sicoco/Minicranebot/stl/wheel base.stl

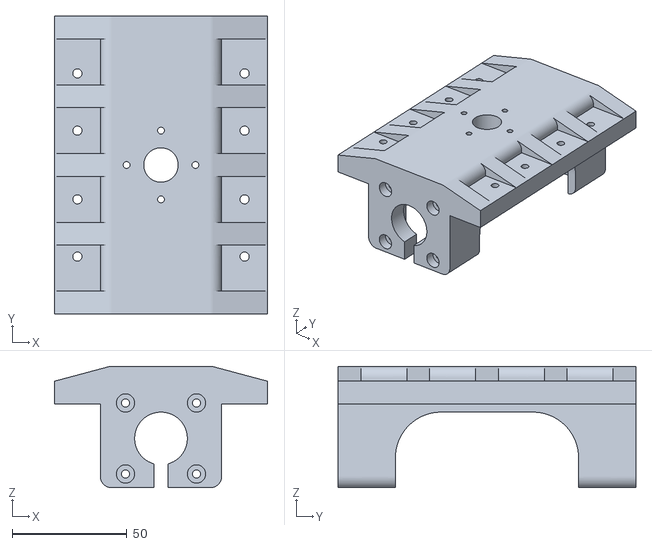
[picture p17: CAD file, 2018-08-06]
stl/wheel base.stl
93.0 x 130.0 x 53.0
