sicoco/Minicranebot/stl/wedge.stl

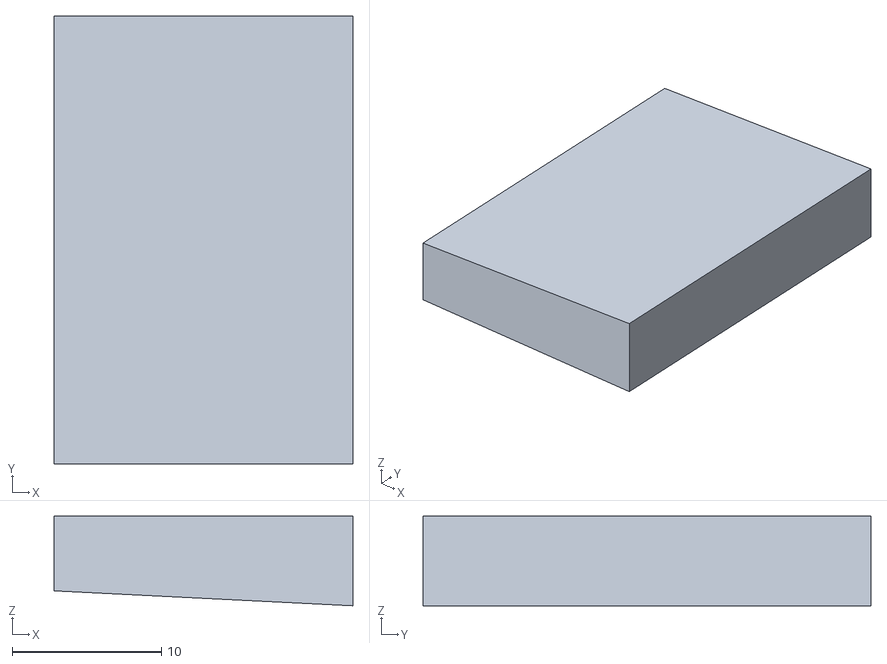
[picture p18: CAD file, 2018-07-30]
stl/wedge.stl
20.0 x 30.0 x 6.00
