sicoco/Minicranebot/stl/wedge v2.stl

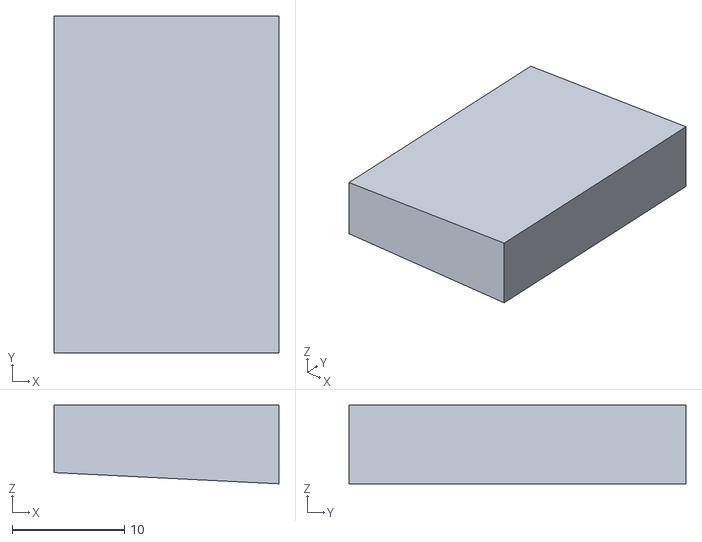
[picture p19: CAD file, 2018-07-30]
stl/wedge v2.stl
20.0 x 30.0 x 7.00
