sicoco/Minicranebot/stl/flex gripper mirror.stl

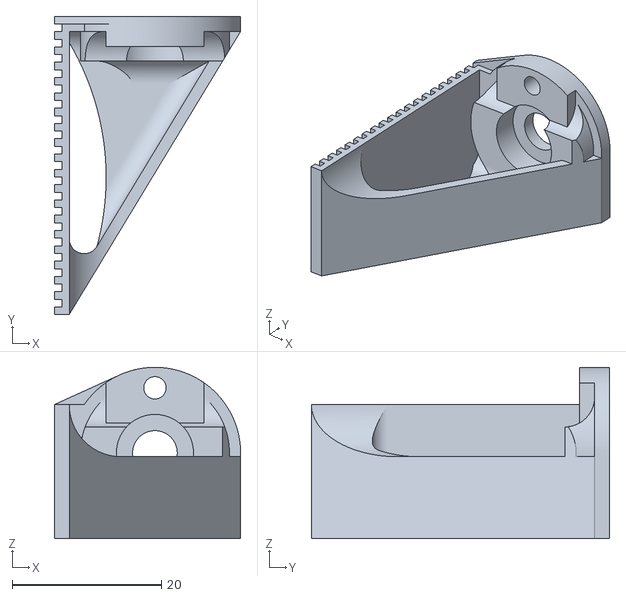
[picture p20: CAD file, 2018-07-27]
stl/flex gripper mirror.stl
25.0 x 40.0 x 23.0
