sicoco/Minicranebot/stl/hook.stl

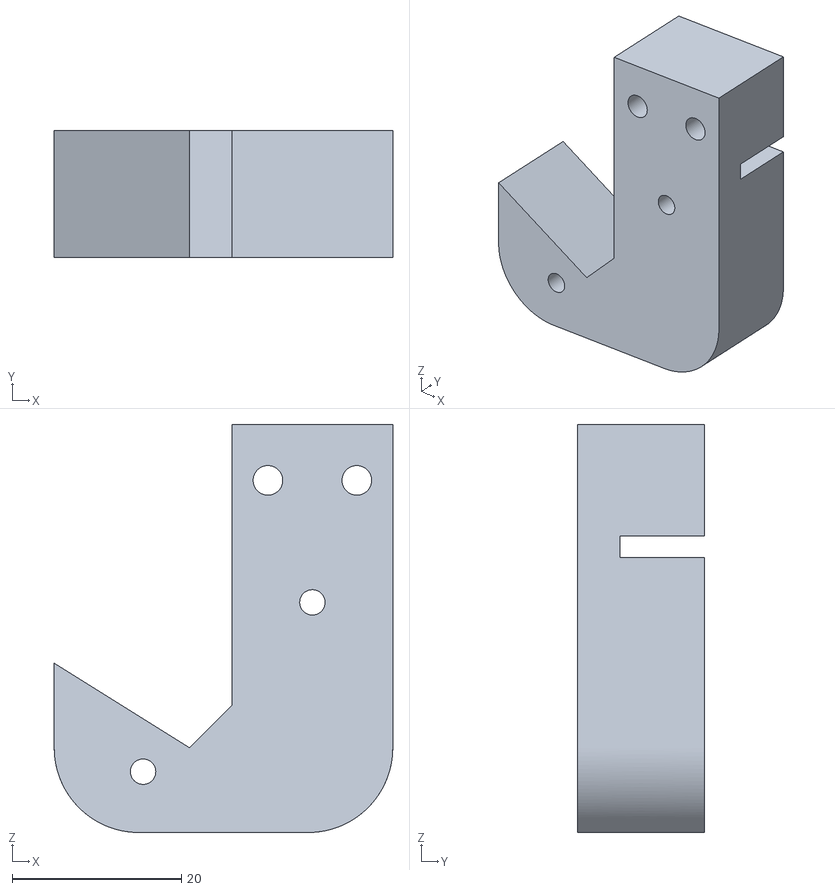
[picture p21: CAD file, 2018-07-27]
stl/hook.stl
40.0 x 15.0 x 48.2
