sicoco/Minicranebot/stl/aligner arm2.stl

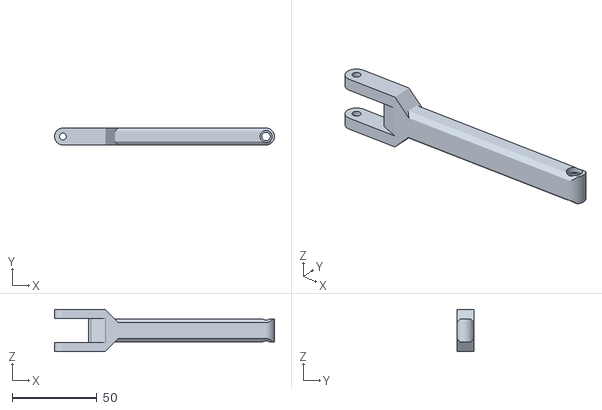
[picture p22: CAD file, 2018-07-27]
stl/aligner arm2.stl
130.0 x 10.0 x 25.0
