sicoco/Minicranebot/stl/waist encoder fixture.stl

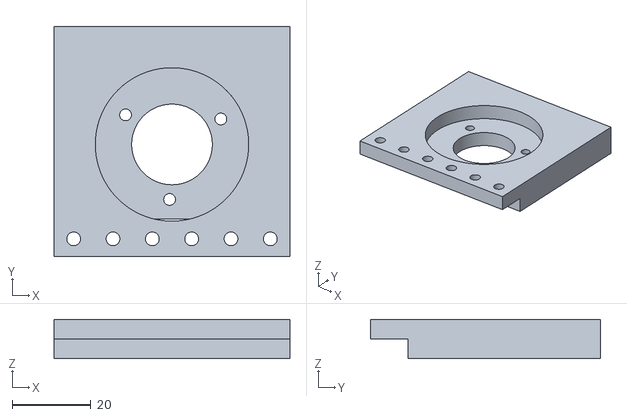
[picture p23: CAD file, 2018-07-27]
stl/waist encoder fixture.stl
60.0 x 58.5 x 10.00
