sicoco/Minicranebot/stl/tentacle block v2.stl

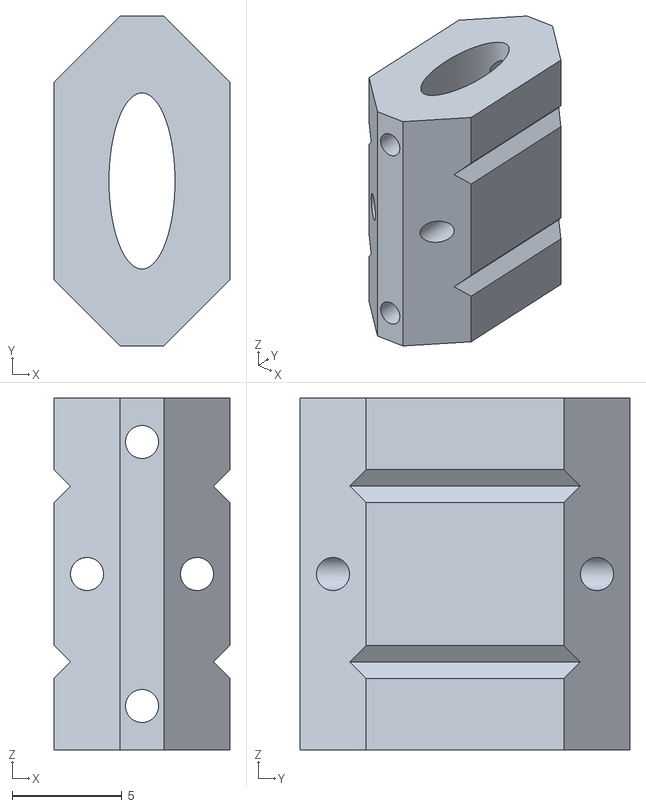
[picture p24: CAD file, 2018-07-27]
stl/tentacle block v2.stl
8.00 x 15.0 x 16.0
