sicoco/Minicranebot/stl/long potentiometer shaft coupler v1.stl

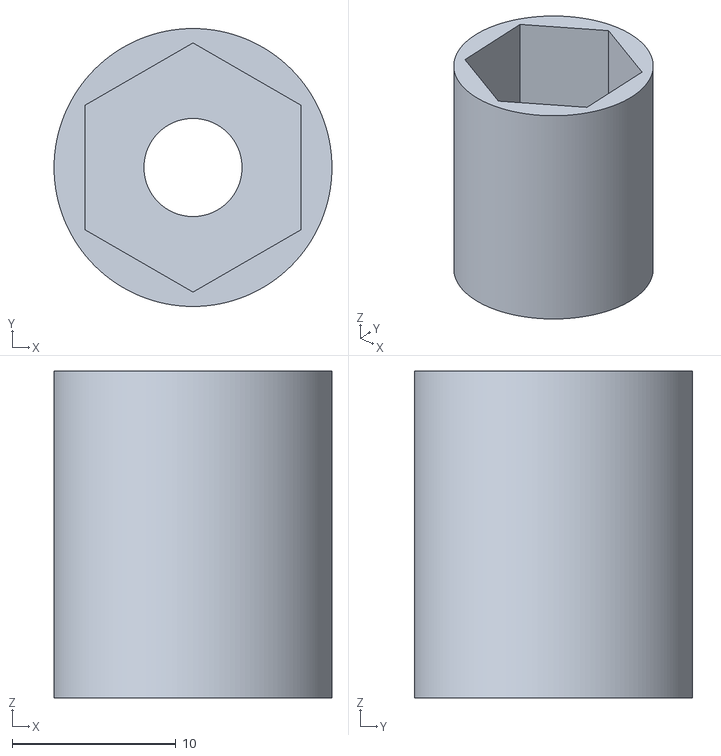
[picture p25: CAD file, 2018-07-27]
stl/long potentiometer shaft coupler v1.stl
17.0 x 17.0 x 20.0
