sicoco/Minicranebot/stl/new finger tip mirror.stl

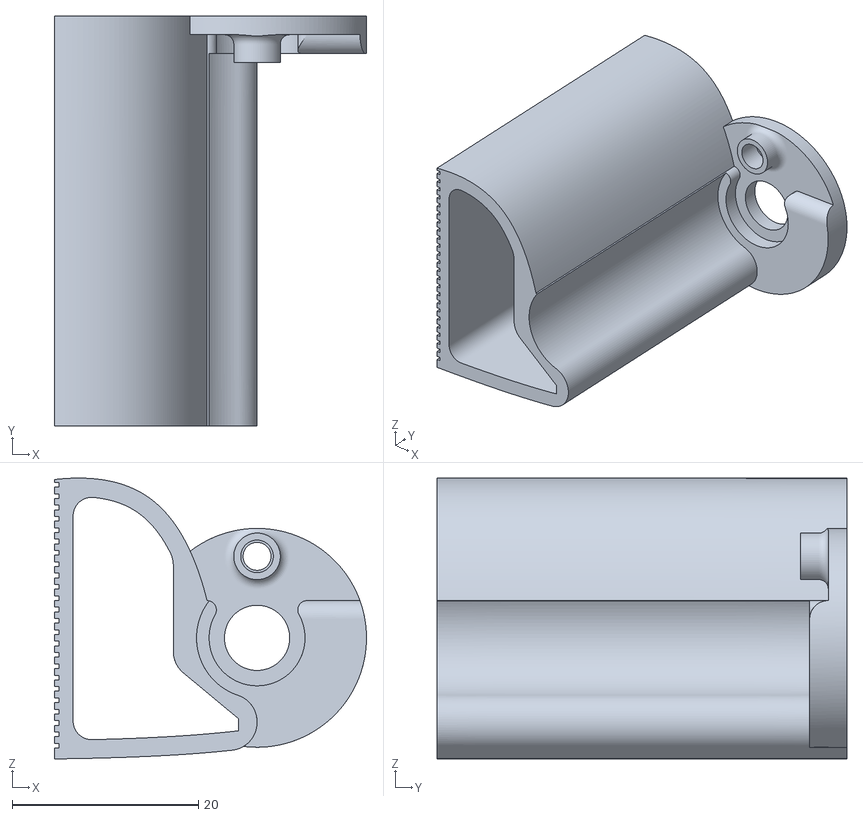
[picture p26: CAD file, 2018-07-27]
stl/new finger tip mirror.stl
33.5 x 44.0 x 30.2
