sicoco/Minicranebot/stl/servo arm.stl

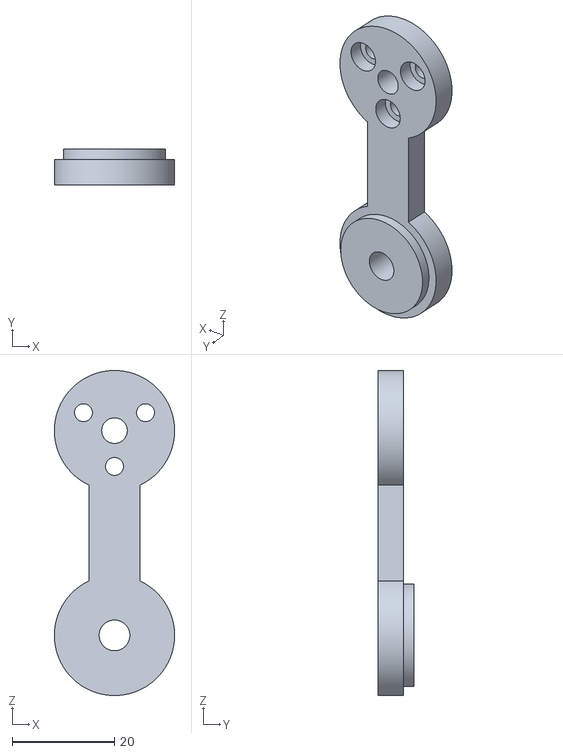
[picture p27: CAD file, 2018-07-27]
stl/servo arm.stl
23.5 x 7.00 x 63.5
