sicoco/Minicranebot/stl/spacer 3.5mm.stl

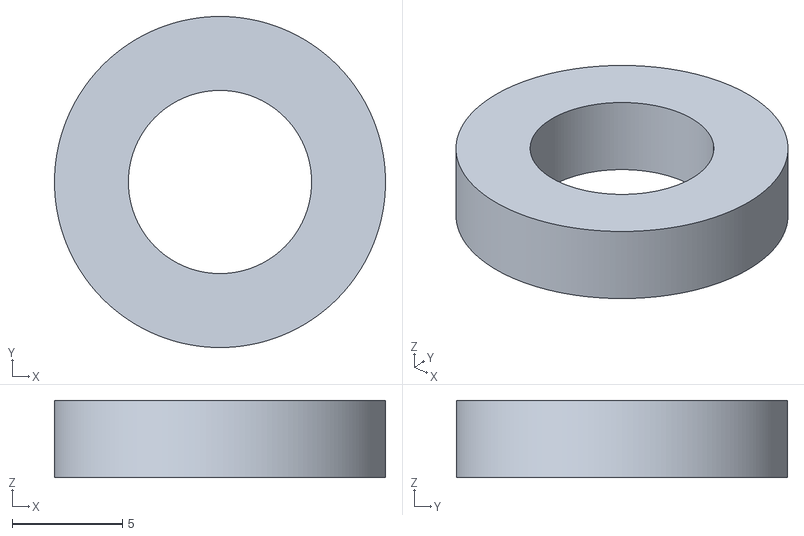
[picture p28: CAD file, 2018-07-27]
stl/spacer 3.5mm.stl
15.0 x 15.0 x 3.50
