sicoco/Minicranebot/stl/potentiometer shaft coupler.stl

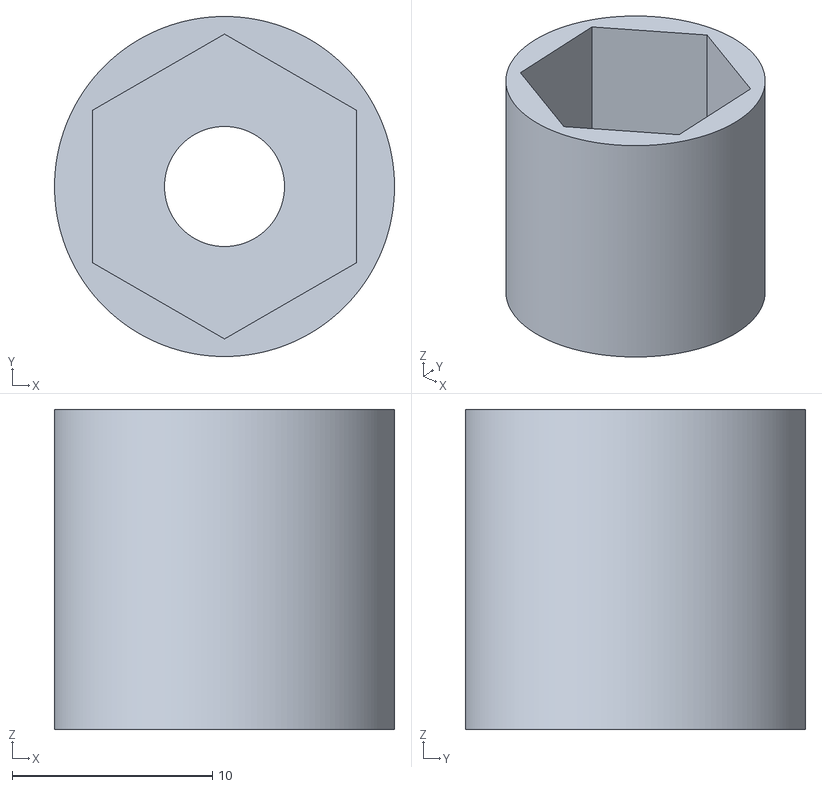
[picture p29: CAD file, 2018-07-27]
stl/potentiometer shaft coupler.stl
17.0 x 17.0 x 16.0
