sicoco/Minicranebot/stl/Body2.stl

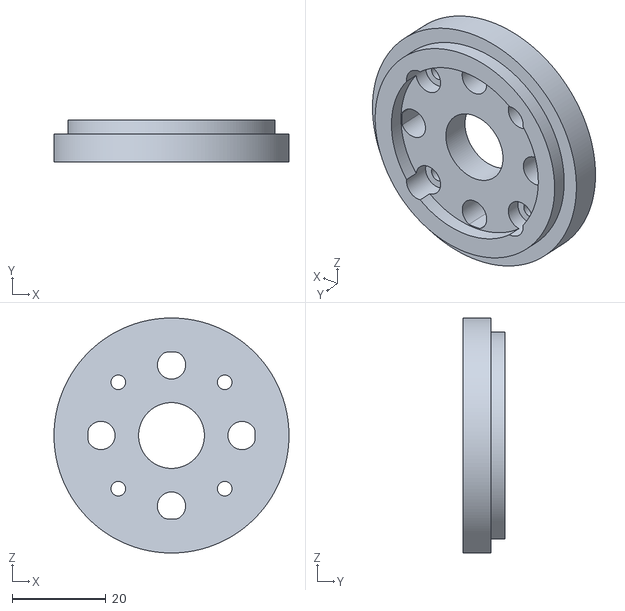
[picture p30: CAD file, 2018-07-27]
stl/Body2.stl
50.0 x 9.00 x 50.0
