sicoco/Minicranebot/stl/rack and wrist holder.stl

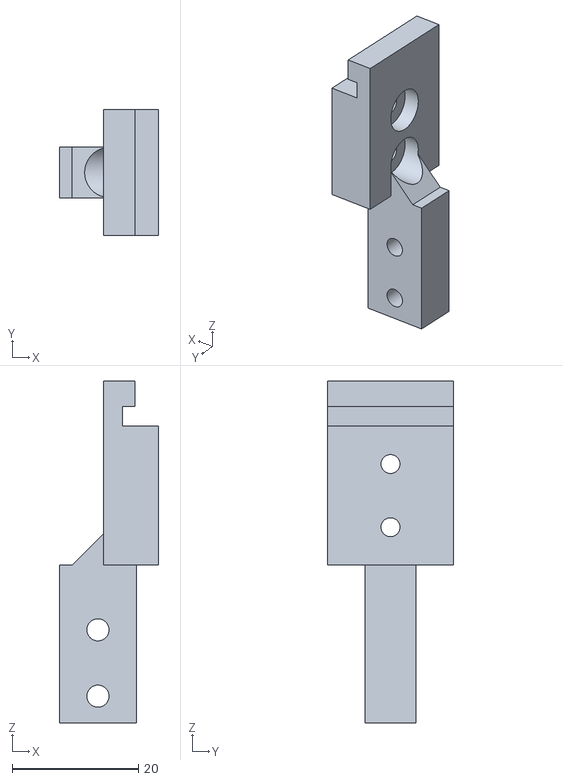
[picture p31: CAD file, 2018-07-27]
stl/rack and wrist holder.stl
15.7 x 20.0 x 54.1
