sicoco/Minicranebot/stl/hook cover.stl

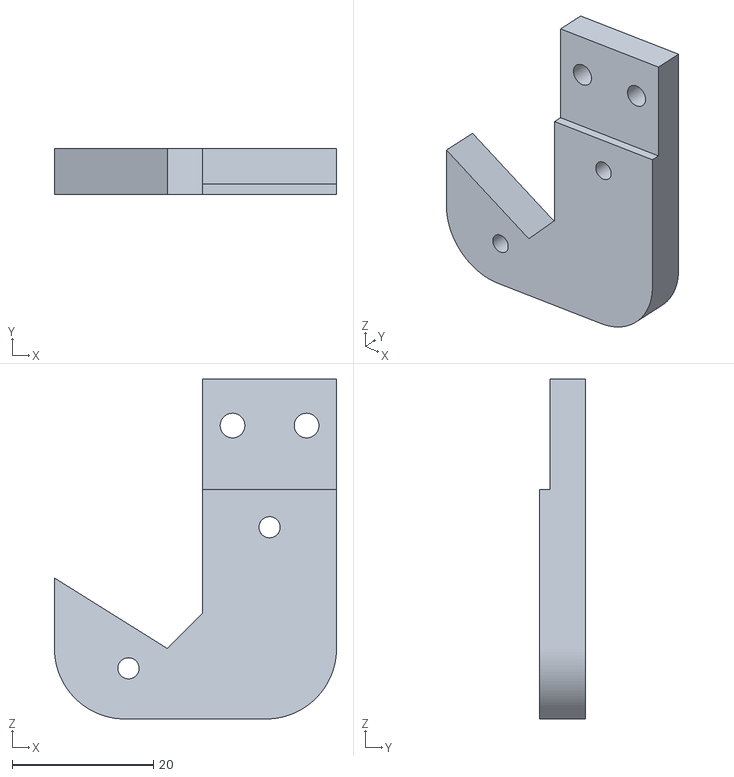
[picture p32: CAD file, 2018-07-27]
stl/hook cover.stl
40.0 x 6.50 x 48.2
