sicoco/Minicranebot/stl/counterweight motor fixture.stl

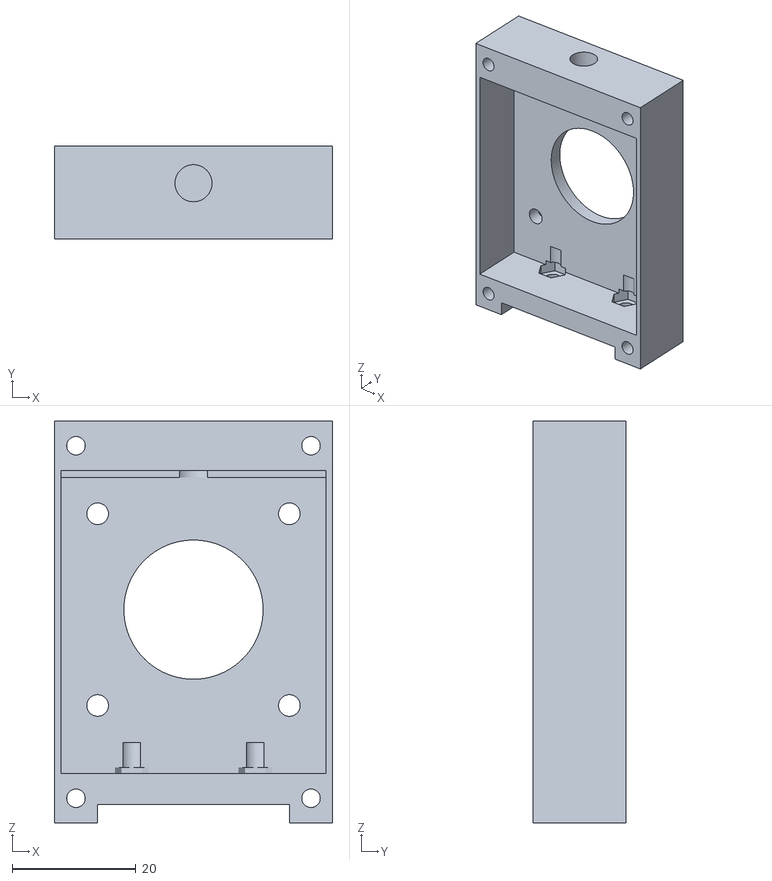
[picture p33: CAD file, 2018-07-27]
stl/counterweight motor fixture.stl
45.0 x 15.0 x 65.0
