sicoco/Minicranebot/stl/waist tall spacer.stl

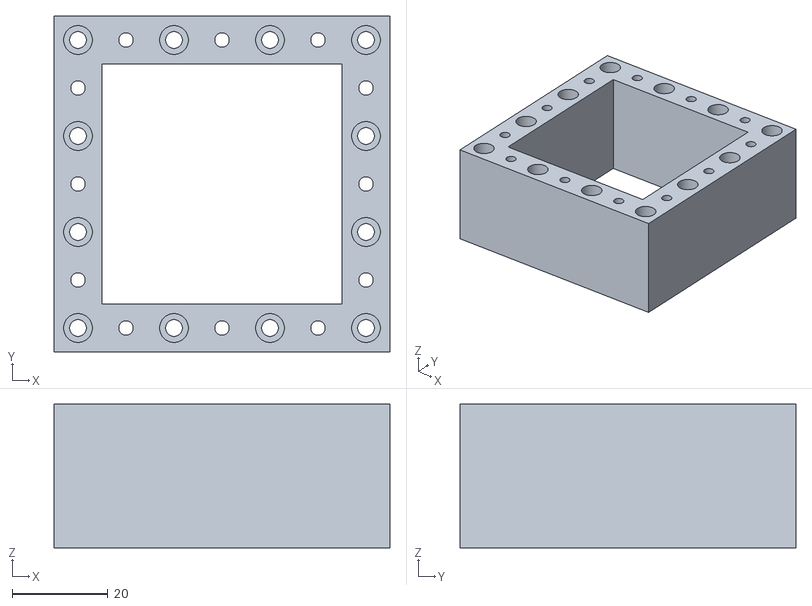
[picture p34: CAD file, 2018-07-27]
stl/waist tall spacer.stl
70.0 x 70.0 x 30.0
