sicoco/Minicranebot/stl/pulley_GT2 70T timingpulley v18_Body1_.stl

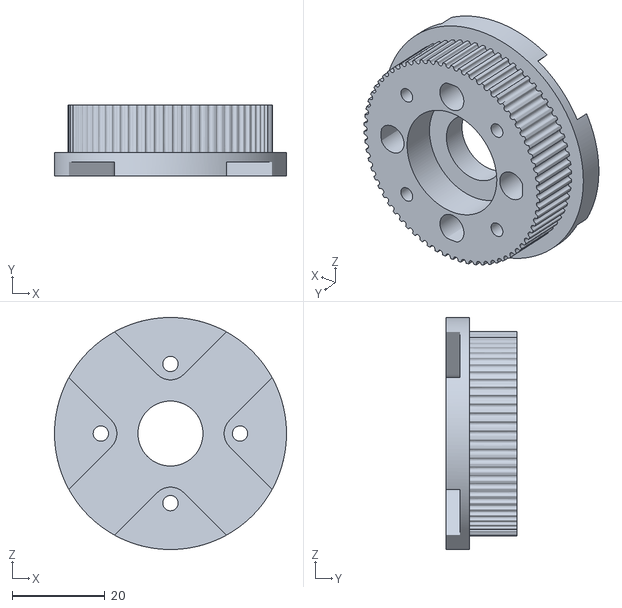
[picture p35: CAD file, 2018-07-27]
stl/pulley_GT2 70T timingpulley v18_Body1_.stl
50.0 x 15.2 x 50.0
