sicoco/Minicranebot/stl/fan shield short.stl

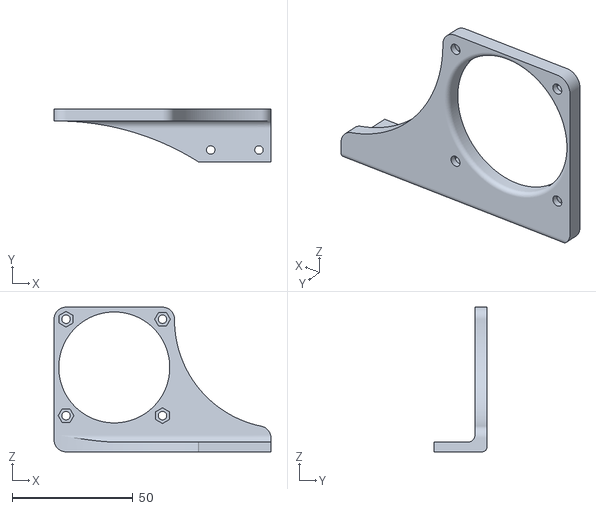
[picture p36: CAD file, 2018-07-27]
stl/fan shield short.stl
90.0 x 22.0 x 60.0
