sicoco/Minicranebot/stl/aligner arm1.stl

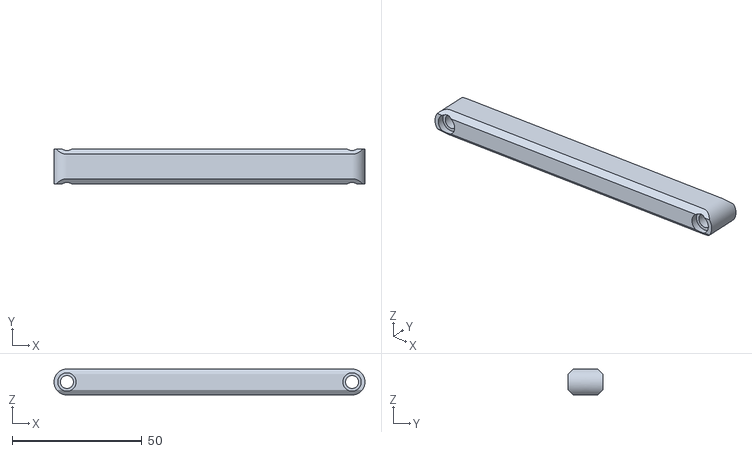
[picture p37: CAD file, 2018-07-27]
stl/aligner arm1.stl
120.0 x 13.5 x 10.0
