sicoco/Minicranebot/stl/counterweight fixture.stl

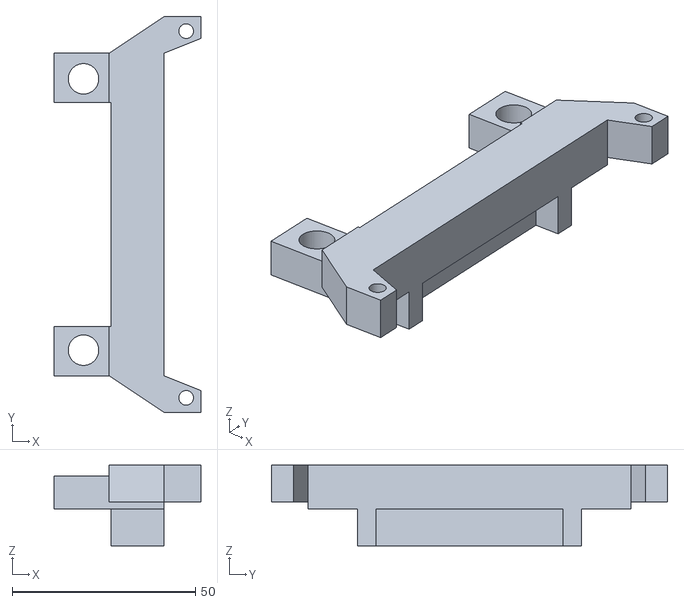
[picture p38: CAD file, 2018-07-27]
stl/counterweight fixture.stl
40.0 x 108.0 x 22.0
