sicoco/Minicranebot/stl/payload fixture.stl

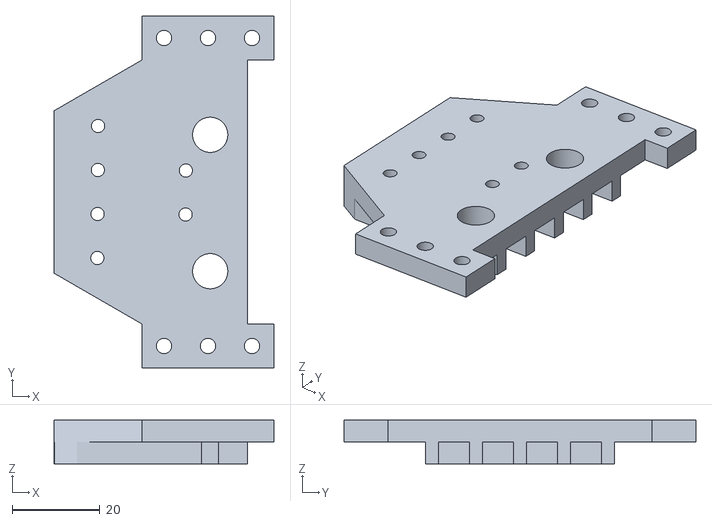
[picture p39: CAD file, 2018-07-27]
stl/payload fixture.stl
50.0 x 80.0 x 10.0
