sicoco/Minicranebot/stl/60T M1 Internal Gear Bowden_60T M1 Internal Gear Bowden v7_Body1_60T M1 Internal Gear.stl

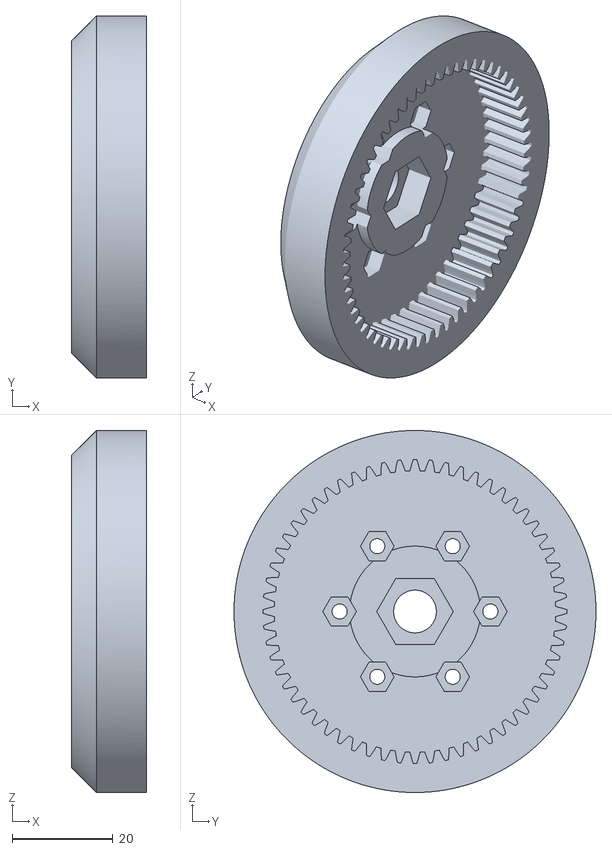
[picture p40: CAD file, 2018-07-27]
stl/60T M1 Internal Gear Bowden_60T M1 Internal Gear Bowden v7_Body1_60T M1 Internal Gear.stl
15.0 x 72.0 x 72.0
