sicoco/Minicranebot/stl/Spur Gear (16 teeth m1.5 20deg).stl

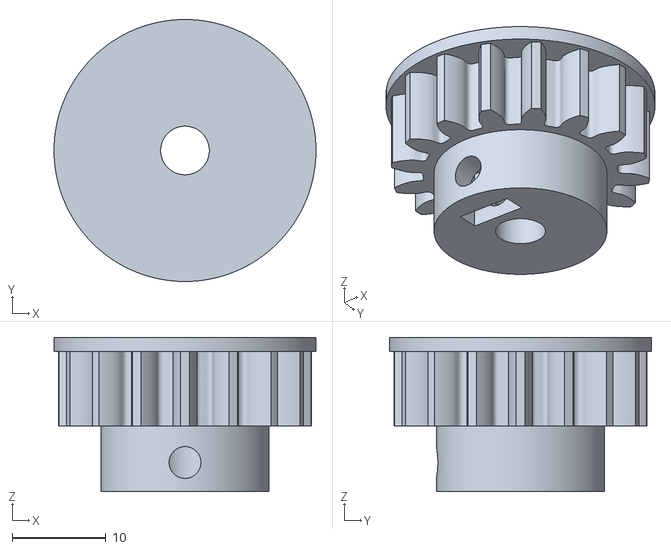
[picture p41: CAD file, 2018-07-27]
stl/Spur Gear (16 teeth m1.5 20deg).stl
28.0 x 28.0 x 16.5
