sicoco/Minicranebot/stl/60T M1 Internal Gear.stl

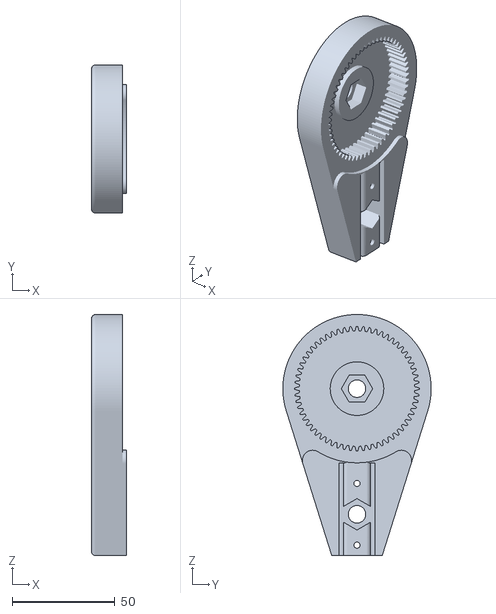
[picture p42: CAD file, 2018-07-27]
stl/60T M1 Internal Gear.stl
17.0 x 72.0 x 117.0
