sicoco/Minicranebot/stl/14T M1 Crossed  Planet gear.stl

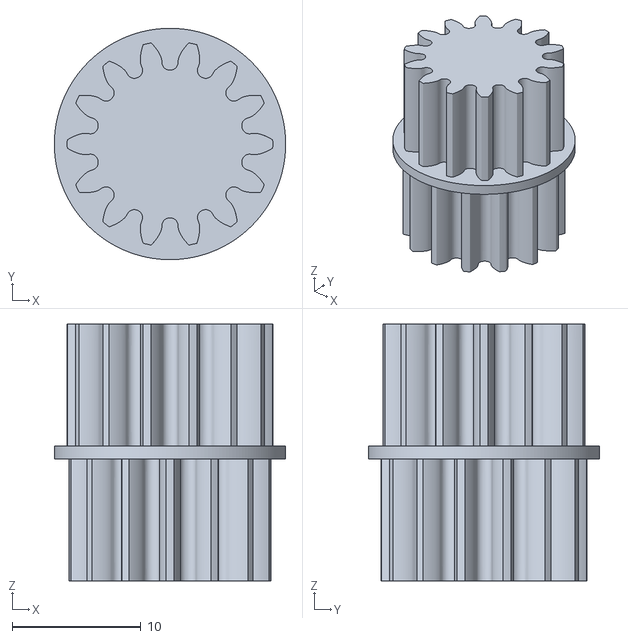
[picture p43: CAD file, 2018-07-27]
stl/14T M1 Crossed Planet gear.stl
18.0 x 18.0 x 20.0
