sicoco/Minicranebot/stl/elbow joint opposite side v3.stl

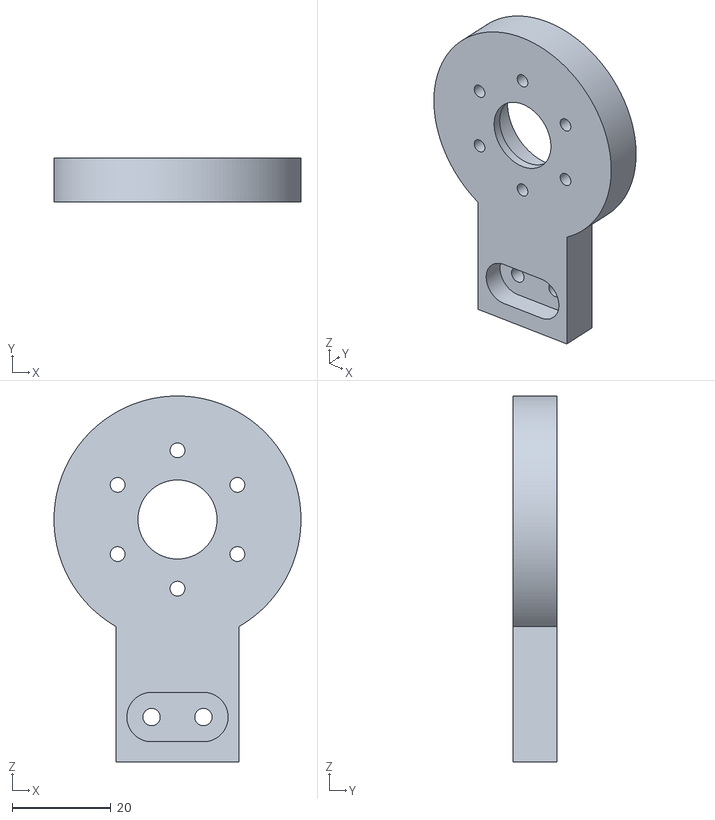
[picture p44: CAD file, 2018-07-27]
stl/elbow joint opposite side v3.stl
50.0 x 9.00 x 74.1
