sicoco/Minicranebot/stl/spur gear 40 & 22 m1.5 20deg.stl

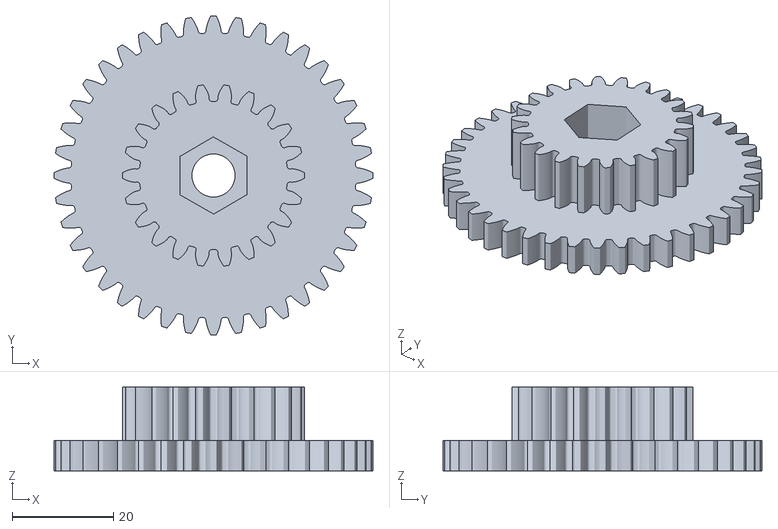
[picture p45: CAD file, 2018-07-27]
stl/spur gear 40 & 22 m1.5 20deg.stl
63.0 x 63.0 x 16.5
