sicoco/Minicranebot/stl/waist spacer2 v4.stl

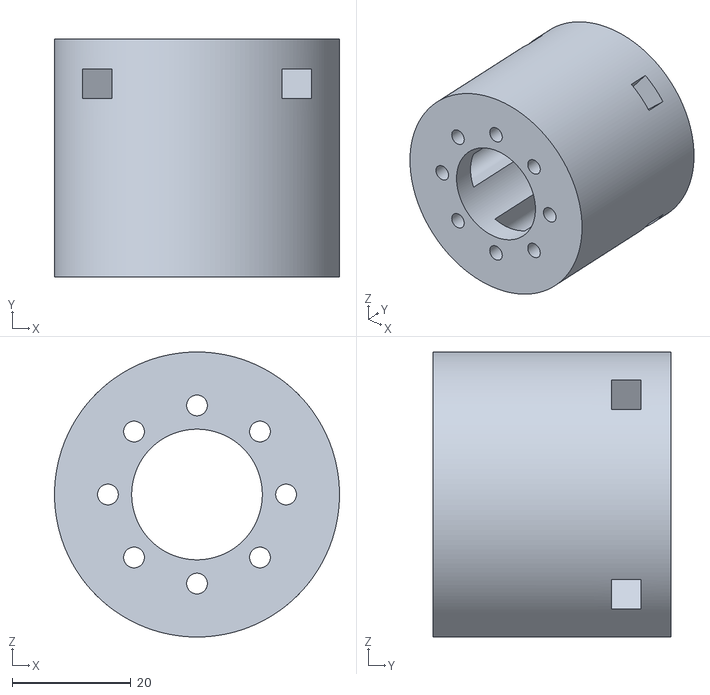
[picture p46: CAD file, 2018-07-27]
stl/waist spacer2 v4.stl
48.0 x 40.0 x 48.0
