sicoco/Minicranebot/stl/Spur Gear (20 teeth).stl

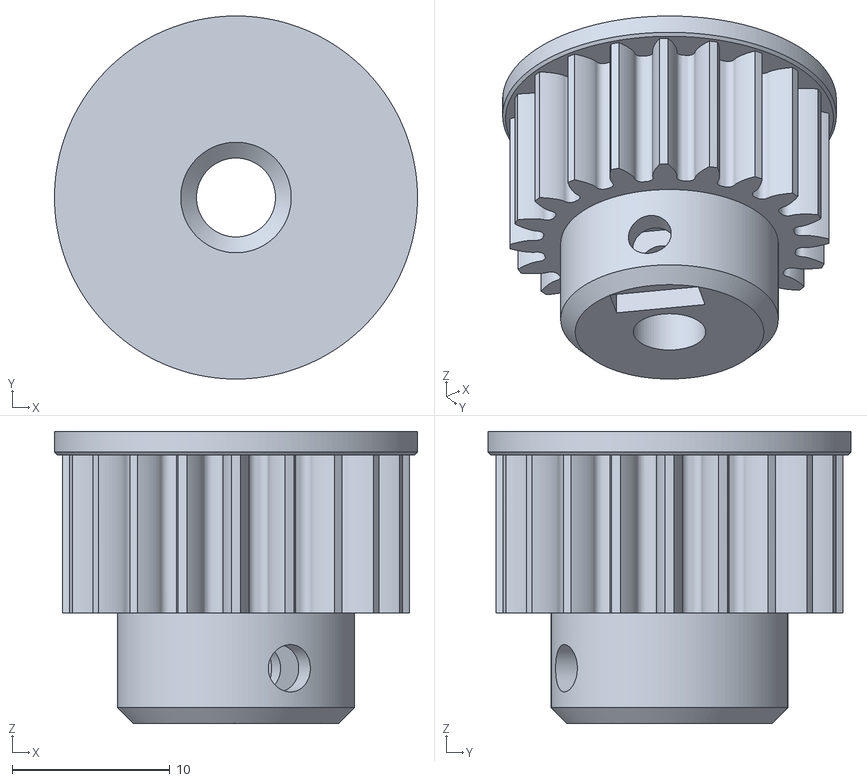
[picture p47: CAD file, 2018-07-27]
stl/Spur Gear (20 teeth).stl
23.0 x 23.0 x 18.5
