sicoco/Minicranebot/stl/block finger half.stl

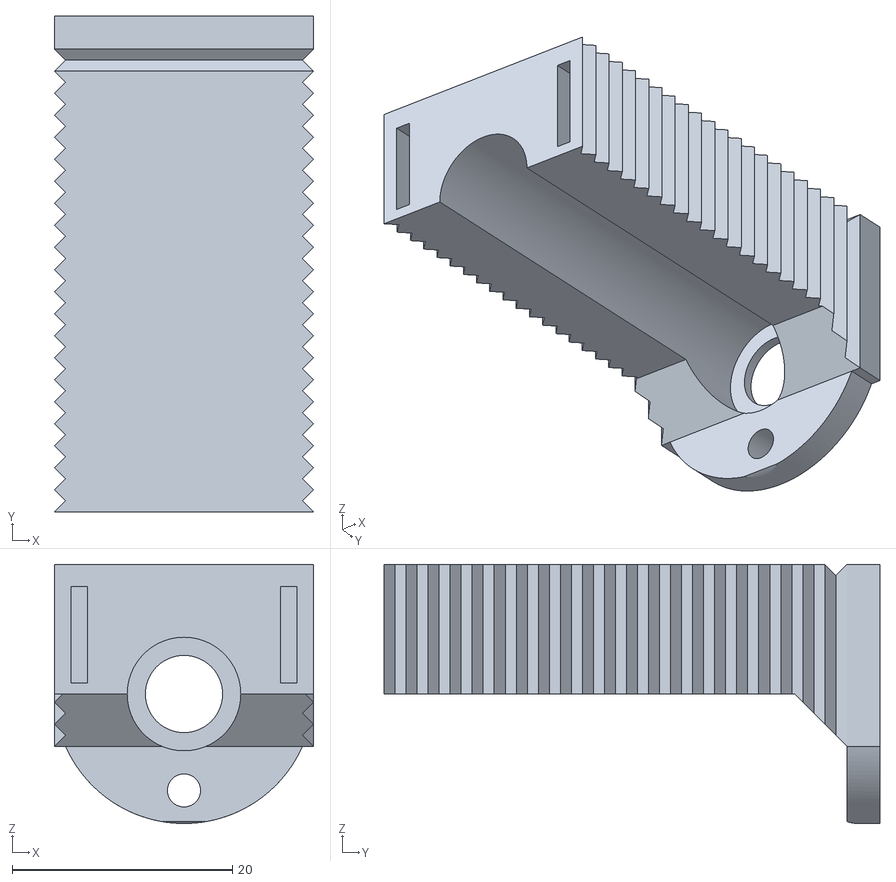
[picture p48: CAD file, 2018-07-27]
stl/block finger half.stl
23.5 x 45.0 x 23.5
