sicoco/Minicranebot/stl/waist.stl

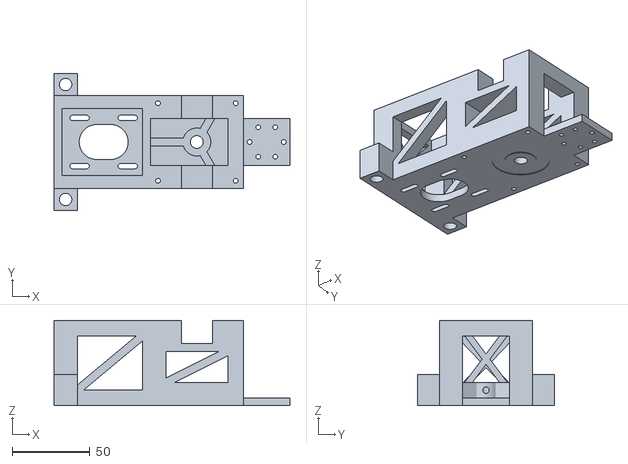
[picture p49: CAD file, 2018-07-27]
stl/waist.stl
152.0 x 88.0 x 55.0
