sicoco/Minicranebot/stl/rack holder.stl

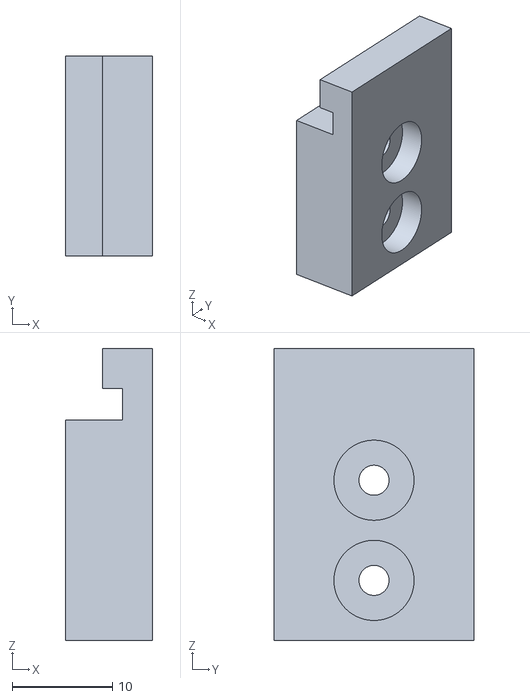
[picture p50: CAD file, 2018-07-27]
stl/rack holder.stl
8.70 x 20.0 x 29.1
