sicoco/Minicranebot/stl/gear box.stl

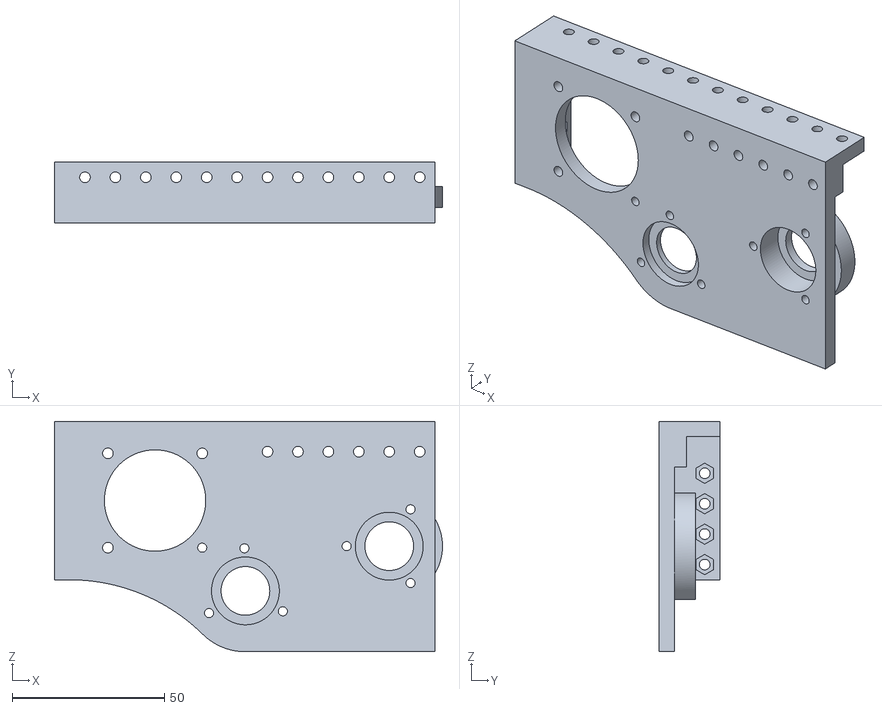
[picture p51: CAD file, 2018-07-27]
stl/gear box.stl
127.5 x 20.0 x 75.7
