sicoco/Minicranebot/stl/encoder gear.stl

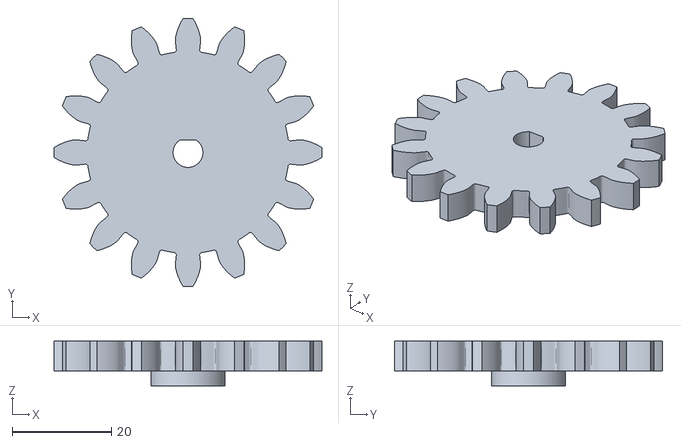
[picture p52: CAD file, 2018-07-27]
stl/encoder gear.stl
54.0 x 54.0 x 9.00
