sicoco/Minicranebot/stl/pulley_GT2 70T timingpulley v18_pulley cap_1_Body1_pulley cap.stl

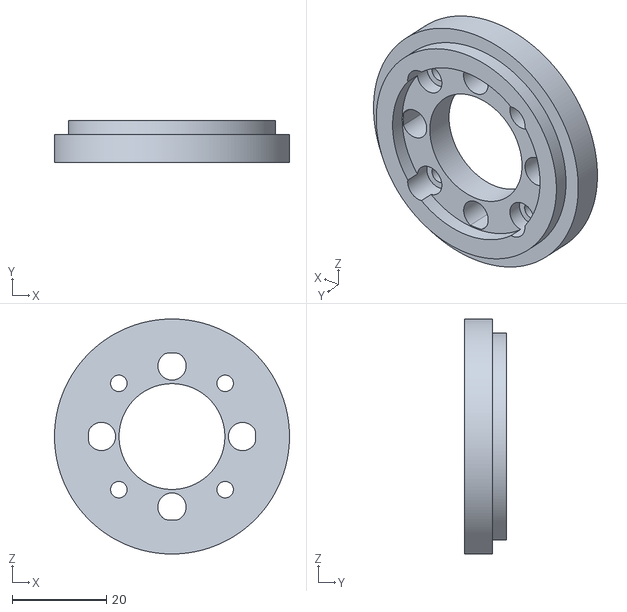
[picture p53: CAD file, 2018-07-27]
stl/pulley_GT2 70T timingpulley v18_pulley cap_1_Body1_pulley cap.stl
50.0 x 9.00 x 50.0
