sicoco/Minicranebot/stl/aligner.stl

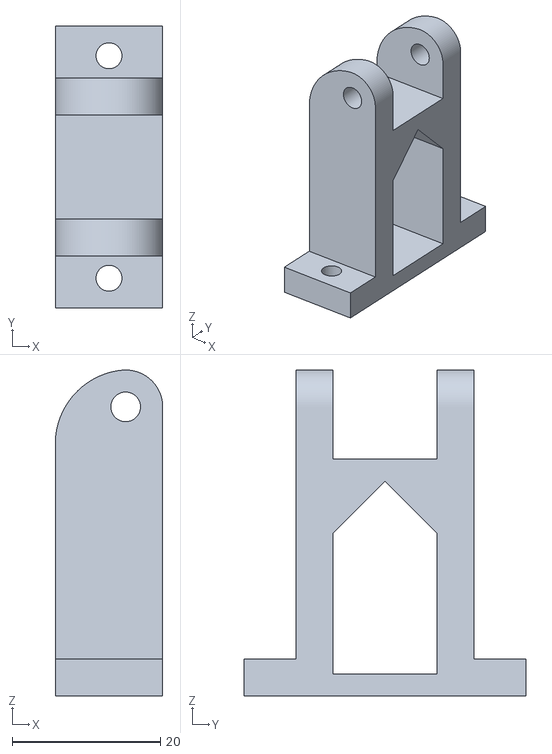
[picture p54: CAD file, 2018-07-27]
stl/aligner.stl
14.5 x 38.0 x 44.0
