sicoco/Minicranebot/stl/battery holder.stl

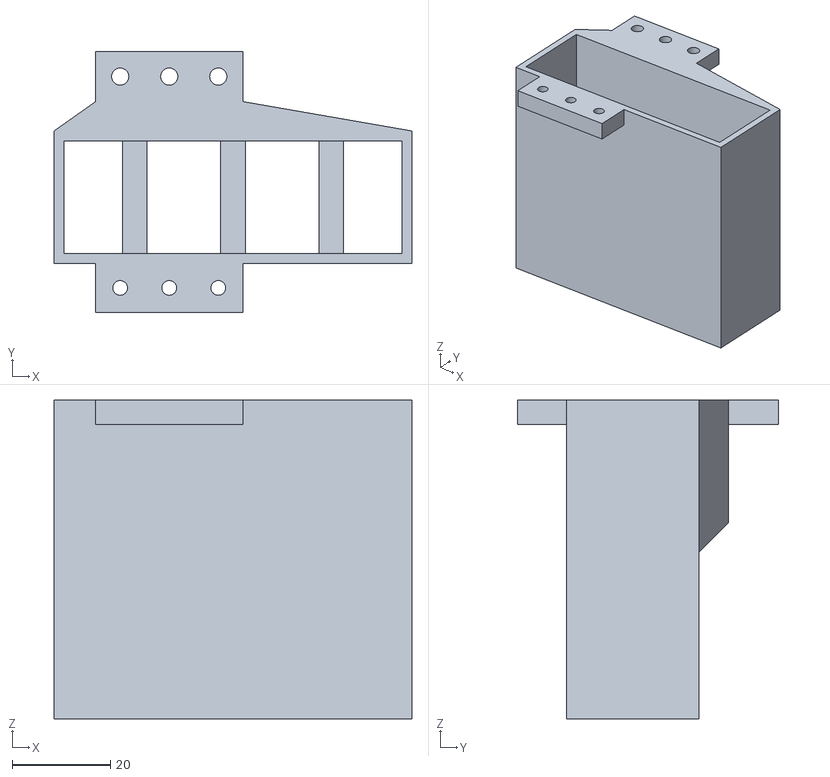
[picture p55: CAD file, 2018-07-27]
stl/battery holder.stl
73.0 x 53.2 x 65.0
