sicoco/Minicranebot/stl/bearing support.stl

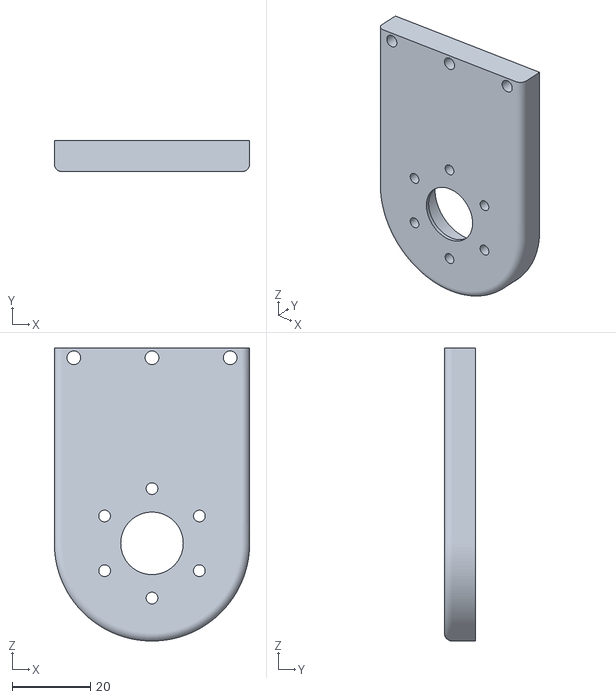
[picture p56: CAD file, 2018-07-27]
stl/bearing support.stl
50.0 x 8.00 x 75.0
