sicoco/Minicranebot/stl/GT2 70T timingpulley v23_base chassis another plan 4 v76_pulley_1_pulley cap_1_Body1_pulley cap.stl

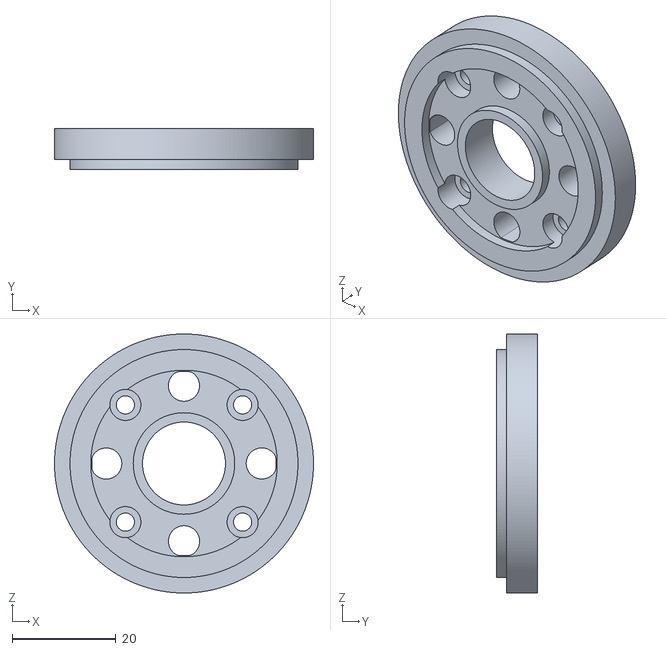
[picture p57: CAD file, 2018-07-27]
stl/GT2 70T timingpulley v23_base chassis another plan 4 v76_pulley_1_pulley cap_1_Body1_pulley cap.stl
50.0 x 8.00 x 50.0
