sicoco/Minicranebot/stl/spool.stl

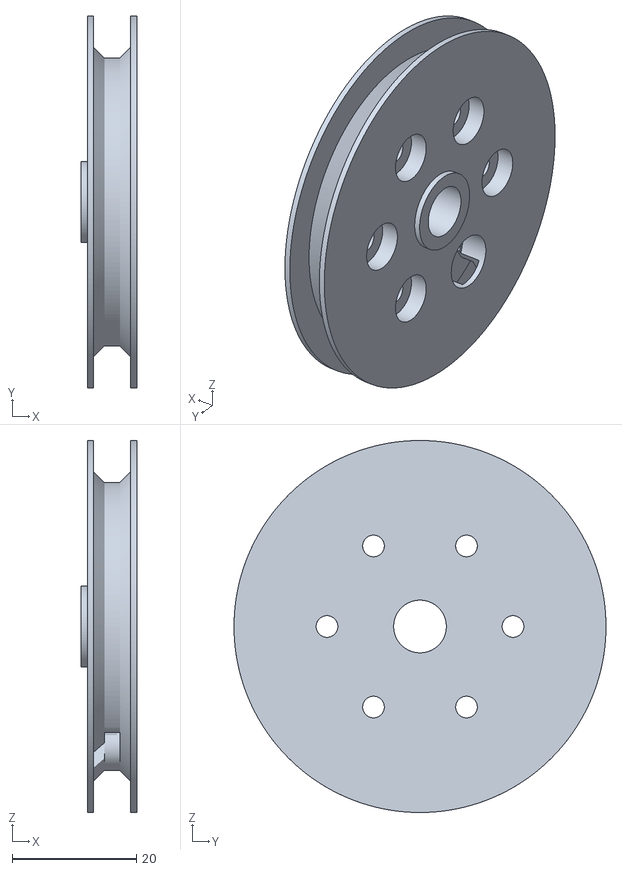
[picture p58: CAD file, 2018-07-27]
stl/spool.stl
9.00 x 60.0 x 60.0
