sicoco/Minicranebot/stl/rack connector v3.stl

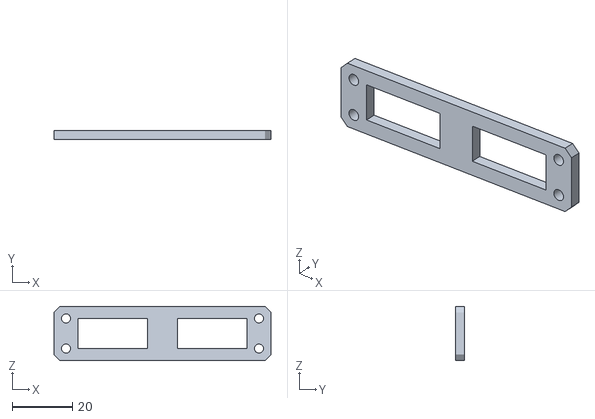
[picture p59: CAD file, 2018-07-27]
stl/rack connector v3.stl
72.0 x 3.00 x 18.0
