sicoco/Minicranebot/stl/Spur Gear (44 teeth m1.5 20deg).stl

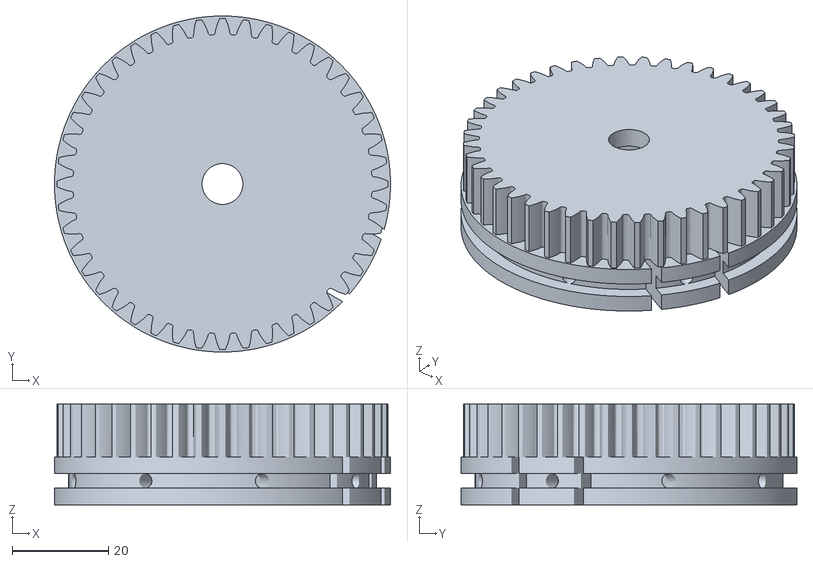
[picture p60: CAD file, 2018-07-27]
stl/Spur Gear (44 teeth m1.5 20deg).stl
70.0 x 70.0 x 21.0
