sicoco/Minicranebot/stl/pin gripper.stl

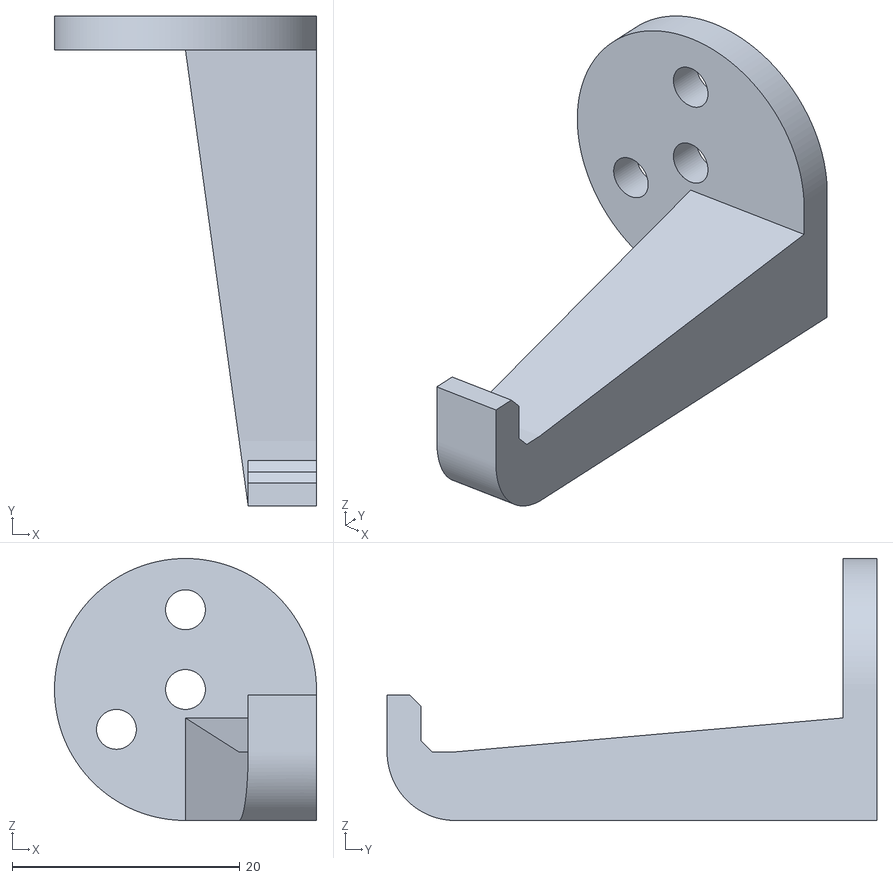
[picture p61: CAD file, 2018-07-27]
stl/pin gripper.stl
23.0 x 43.0 x 23.0
