sicoco/Minicranebot/stl/fan shield.stl

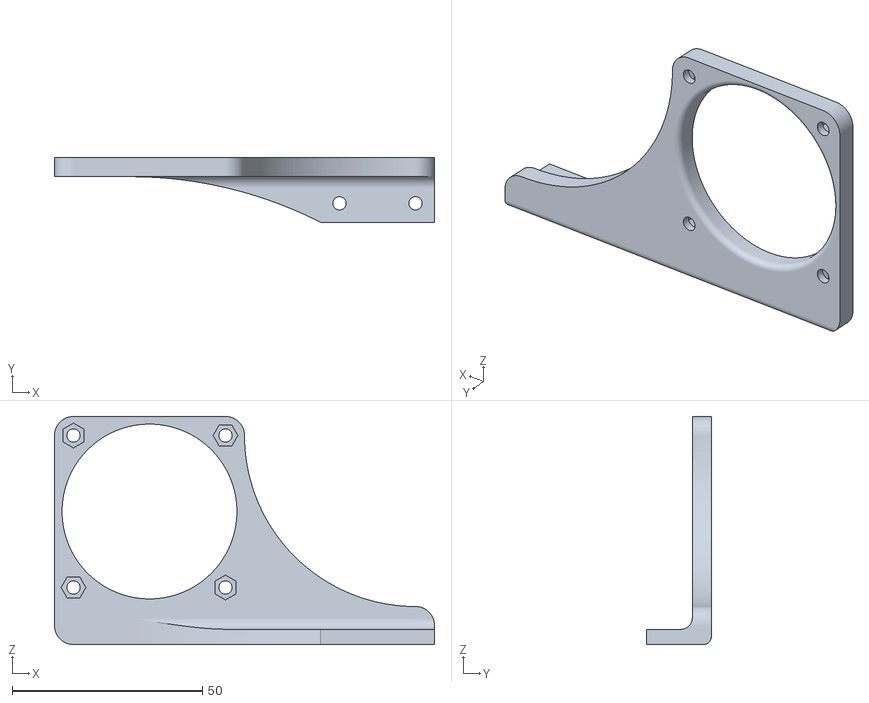
[picture p62: CAD file, 2018-07-27]
stl/fan shield.stl
100.0 x 17.0 x 60.0
