sicoco/Minicranebot/stl/shoulder fixture2 short.stl

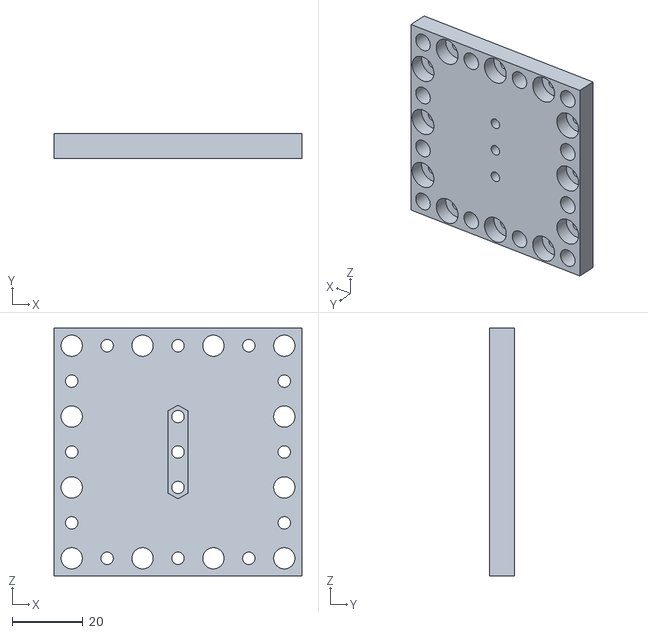
[picture p63: CAD file, 2018-07-27]
stl/shoulder fixture2 short.stl
70.0 x 7.00 x 70.0
