sicoco/Minicranebot/stl/clamp.stl

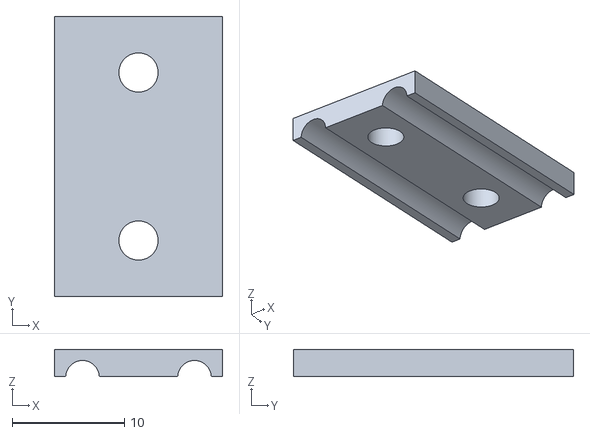
[picture p64: CAD file, 2018-07-27]
stl/clamp.stl
15.0 x 25.0 x 2.45
