sicoco/Minicranebot/stl/gear fixture v2.stl

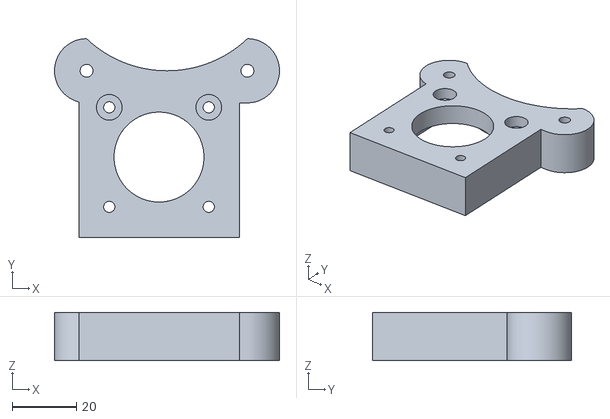
[picture p65: CAD file, 2018-07-27]
stl/gear fixture v2.stl
70.1 x 61.9 x 15.0
