sicoco/Minicranebot/stl/servo gear 20T.stl

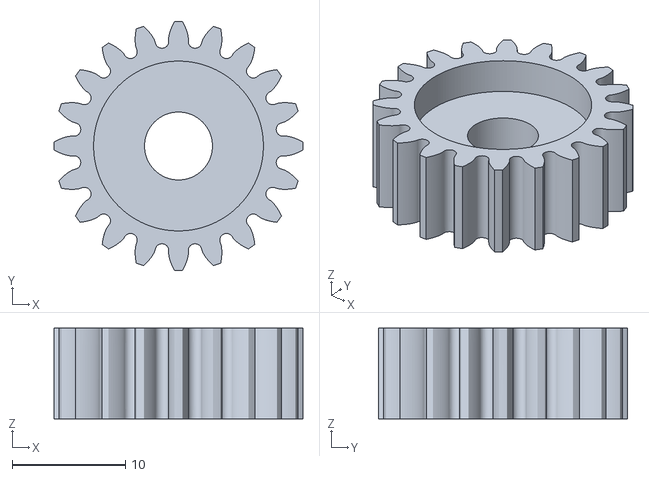
[picture p66: CAD file, 2018-07-27]
stl/servo gear 20T.stl
22.0 x 22.0 x 8.00
