sicoco/Minicranebot/stl/60T M1 Internal Gear Bowden_planetary gearbox bowden cable actuator v9_spool_1_Body1_spool.stl

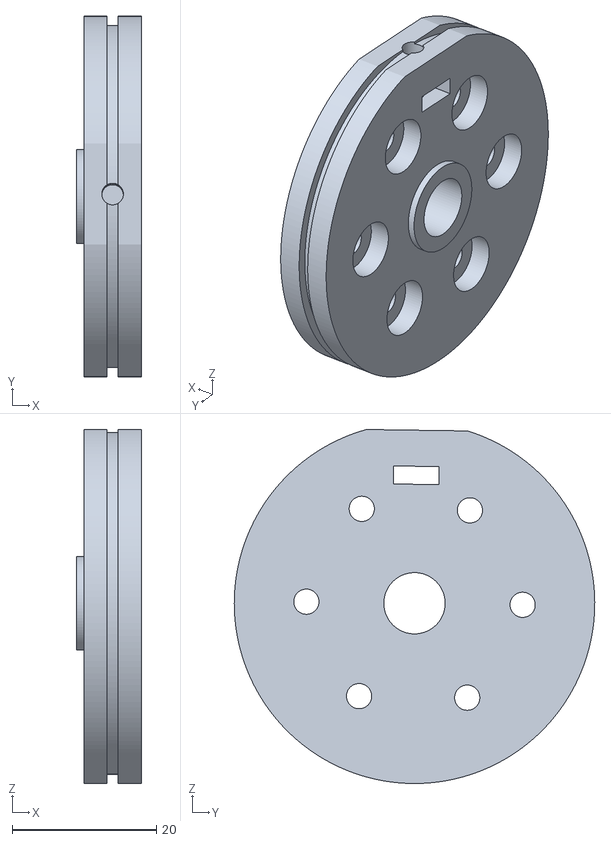
[picture p67: CAD file, 2018-07-27]
stl/60T M1 Internal Gear Bowden_planetary gearbox bowden cable actuator v9_spool_1_Body1_spool.stl
9.00 x 50.0 x 49.1
