sicoco/Minicranebot/stl/58T M1 Internal Gear.stl

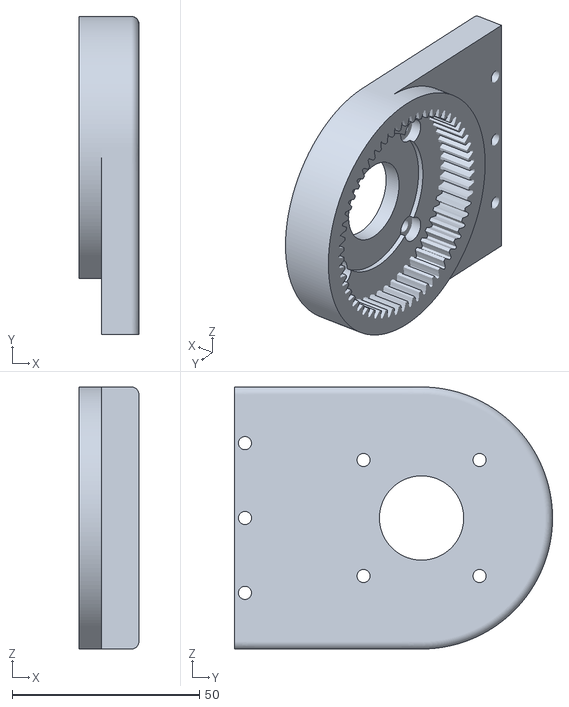
[picture p68: CAD file, 2018-07-27]
stl/58T M1 Internal Gear.stl
16.0 x 85.0 x 70.0
