sicoco/Minicranebot/stl/gearbox separator wide_planetary gearbox bowden cable actuator v9_Body1_gearbox separator wide v4.stl

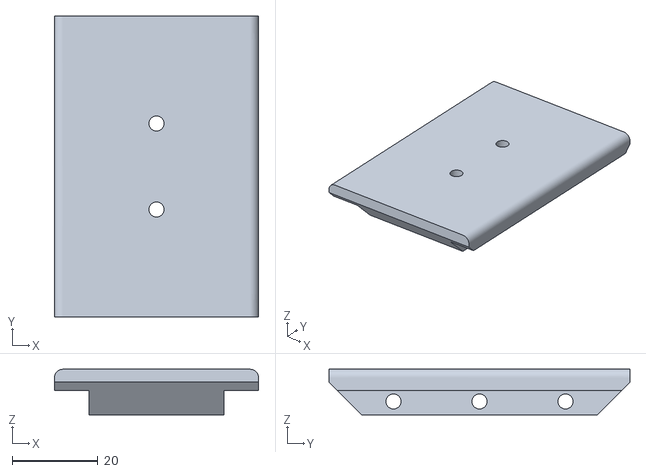
[picture p69: CAD file, 2018-07-27]
stl/gearbox separator wide_planetary gearbox bowden cable actuator v9_Body1_gearbox separator wide v4.stl
47.5 x 70.0 x 10.6
