sicoco/Minicranebot/stl/multifunction finger.stl

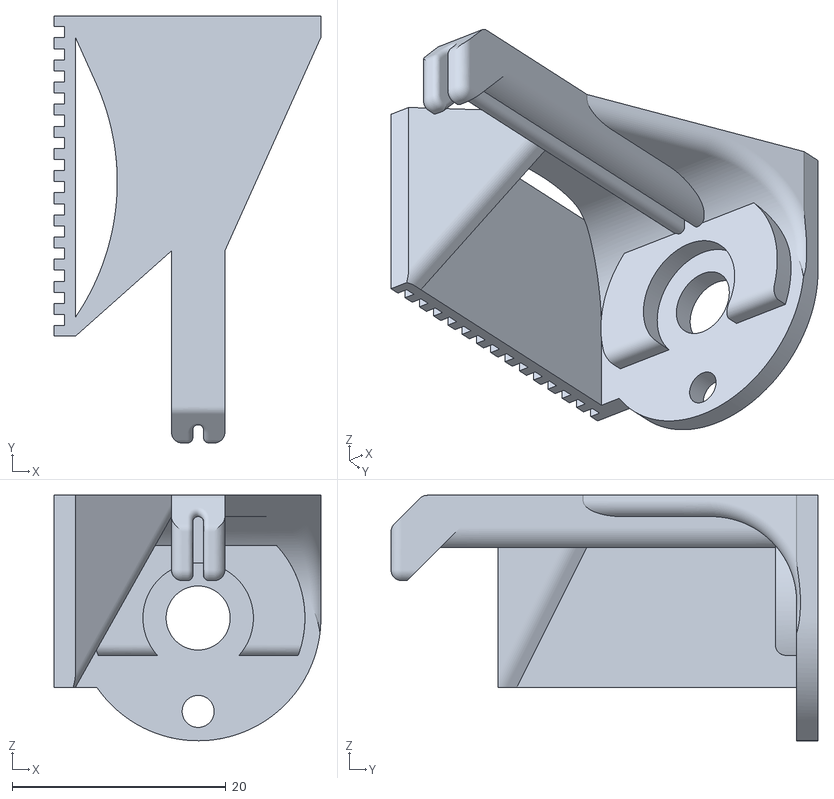
[picture p70: CAD file, 2018-07-27]
stl/multifunction finger.stl
25.0 x 40.0 x 23.0
