sicoco/Minicranebot/stl/spacer 4mm.stl

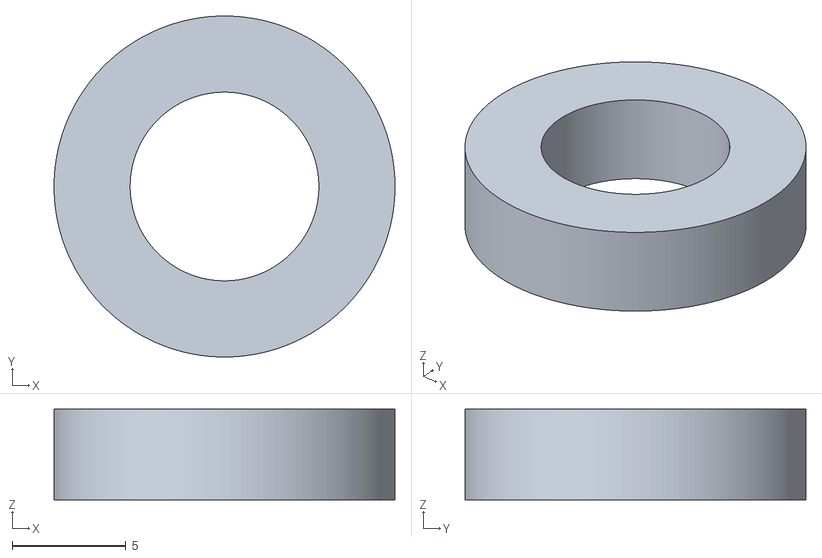
[picture p71: CAD file, 2018-07-27]
stl/spacer 4mm.stl
15.0 x 15.0 x 4.00
