sicoco/Minicranebot/stl/servo arm2.stl

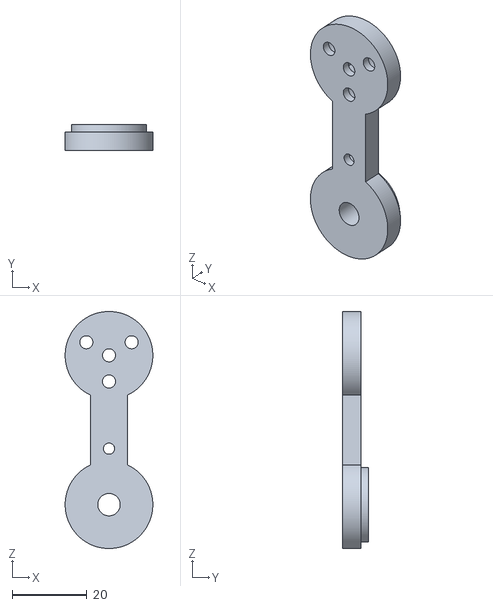
[picture p72: CAD file, 2018-07-27]
stl/servo arm2.stl
23.5 x 7.00 x 63.5
