sicoco/Minicranebot/stl/gear fixture cover.stl

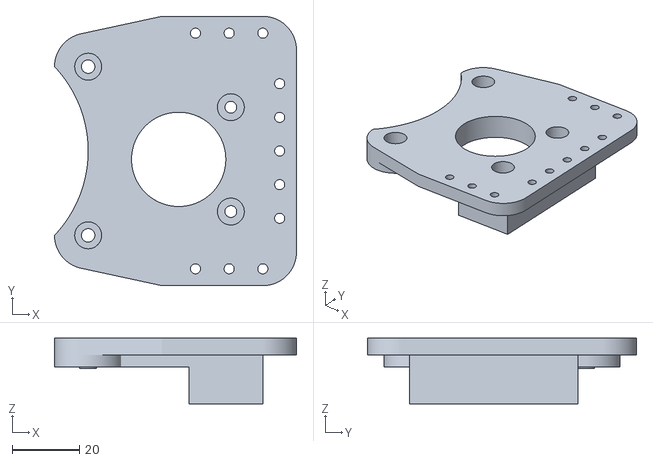
[picture p73: CAD file, 2018-07-27]
stl/gear fixture cover.stl
71.9 x 80.0 x 19.5
