sicoco/Minicranebot/stl/expansion flap.stl

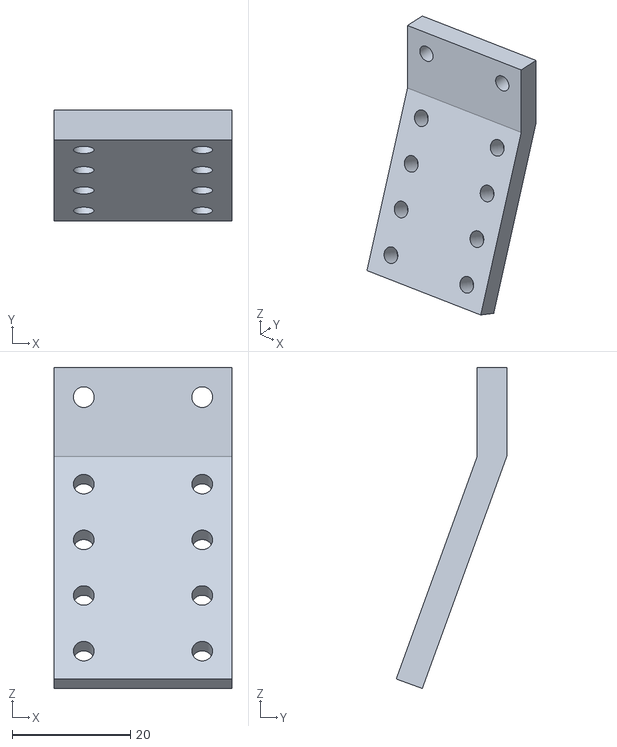
[picture p74: CAD file, 2018-07-27]
stl/expansion flap.stl
30.0 x 18.7 x 54.2
