sicoco/Minicranebot/stl/elbow linkage.stl

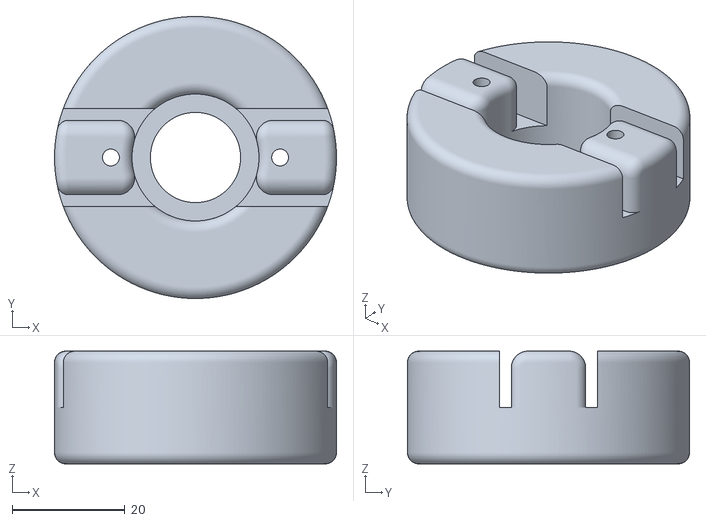
[picture p75: CAD file, 2018-07-27]
stl/elbow linkage.stl
50.0 x 50.0 x 20.0
