sicoco/Minicranebot/stl/extension frame.stl

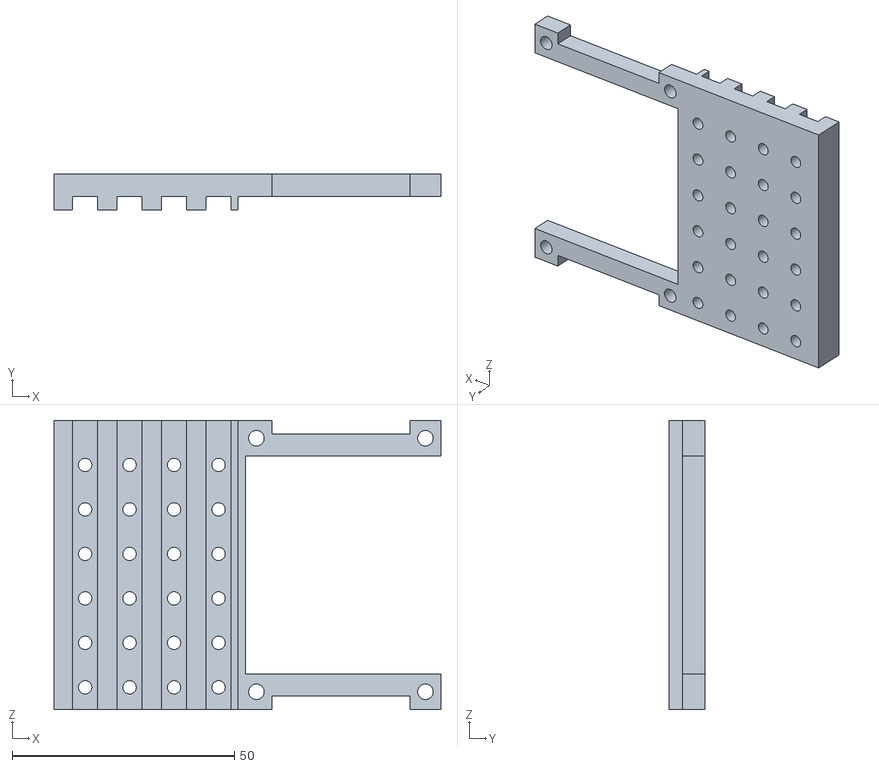
[picture p76: CAD file, 2018-07-27]
stl/extension frame.stl
87.0 x 8.00 x 65.0
