sicoco/Minicranebot/stl/gt2 70tbase.stl

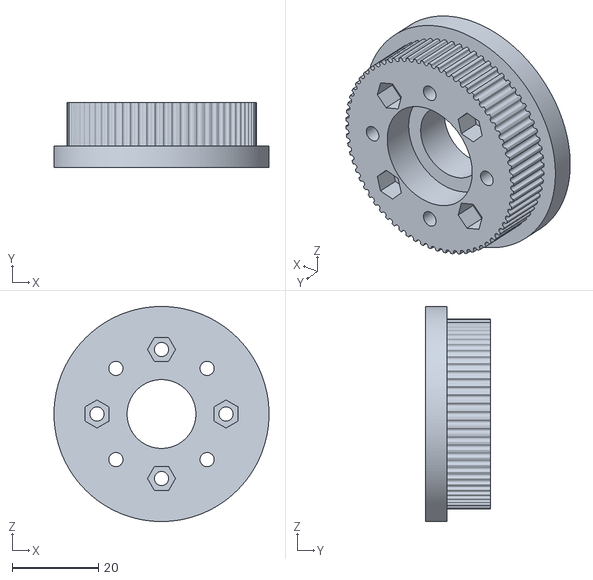
[picture p77: CAD file, 2018-07-27]
stl/gt2 70tbase.stl
50.0 x 15.2 x 50.0
