sicoco/Minicranebot/stl/bowden connector v4.stl

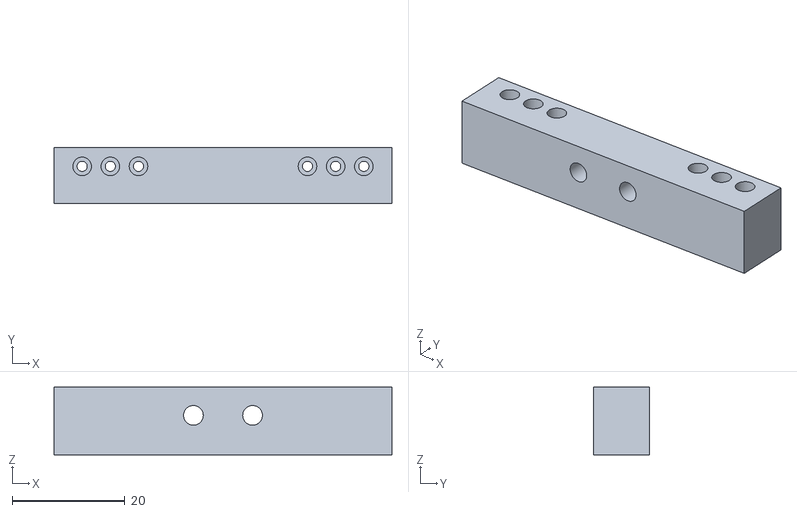
[picture p78: CAD file, 2018-07-27]
stl/bowden connector v4.stl
60.0 x 10.0 x 12.0
