sicoco/Minicranebot/stl/bowden tube holder v6.stl

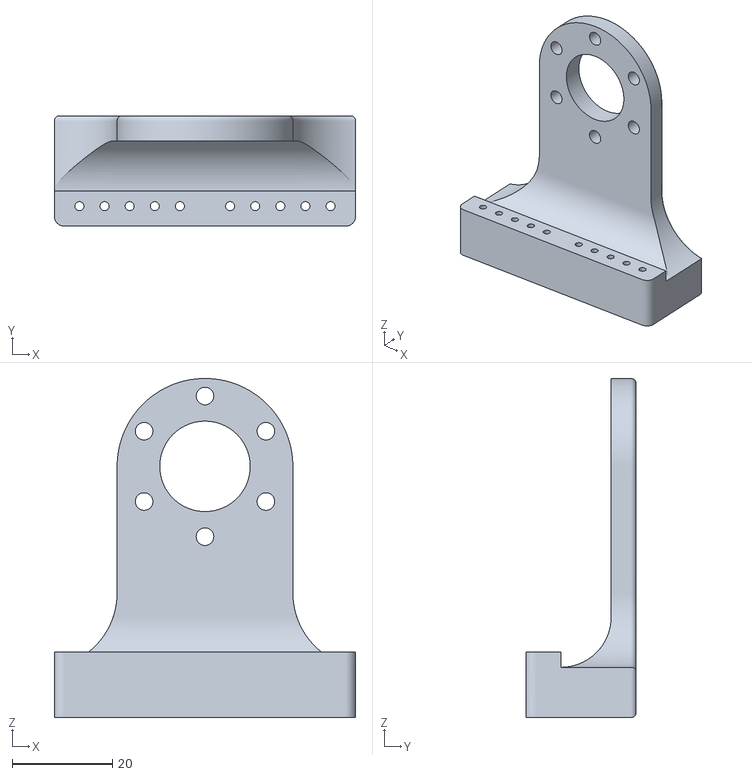
[picture p79: CAD file, 2018-07-27]
stl/bowden tube holder v6.stl
60.0 x 22.0 x 67.5
