sicoco/Minicranebot/stl/aligner2.stl

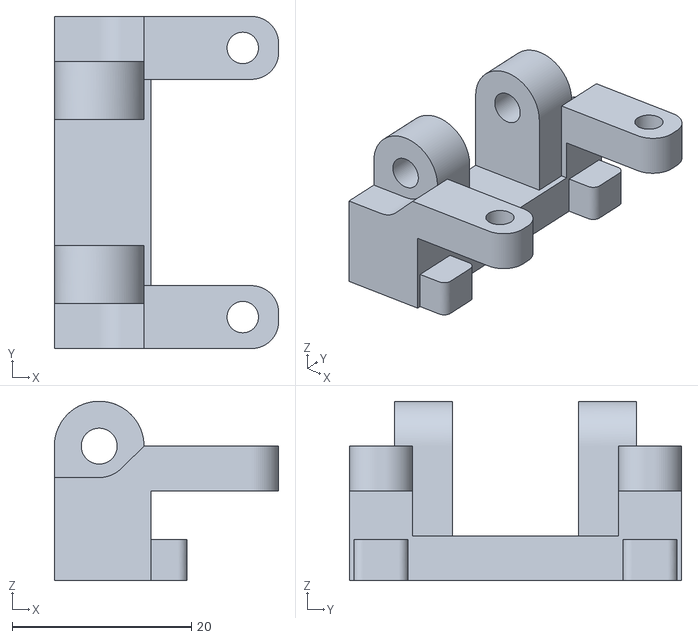
[picture p80: CAD file, 2018-07-27]
stl/aligner2.stl
25.0 x 37.0 x 20.0
