sicoco/Minicranebot/stl/castor cover1.stl

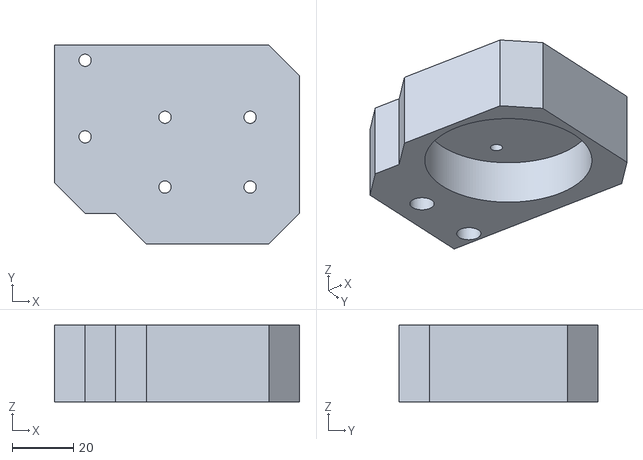
[picture p81: CAD file, 2018-07-27]
stl/castor cover1.stl
80.0 x 65.0 x 25.0
