sicoco/Minicranebot/stl/potentiometer holder.stl

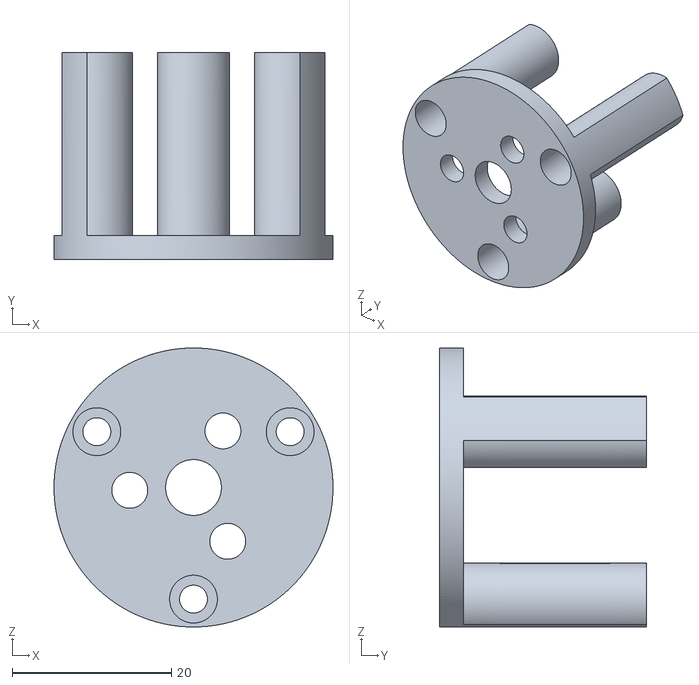
[picture p82: CAD file, 2018-07-27]
stl/potentiometer holder.stl
35.0 x 26.0 x 35.0
