sicoco/Minicranebot/stl/elbow arm link v11.stl

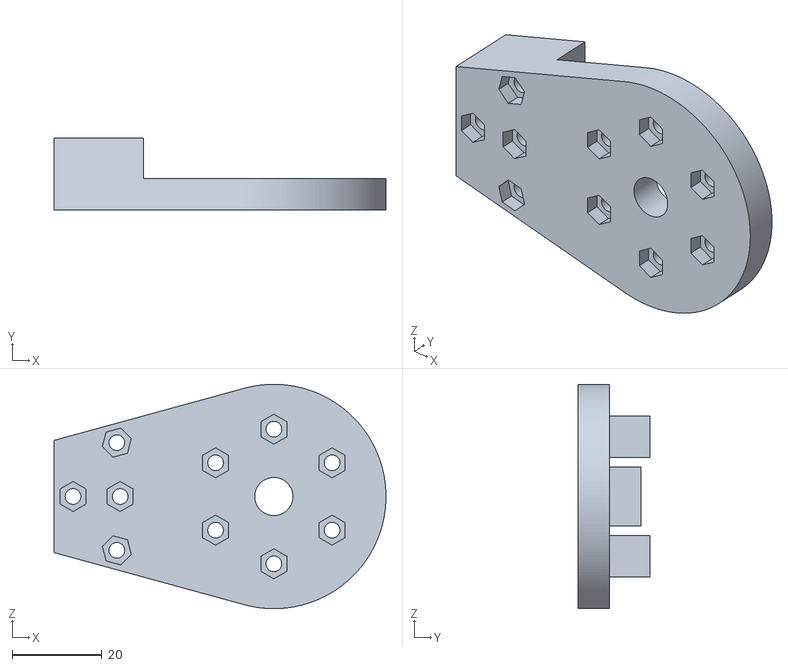
[picture p83: CAD file, 2018-07-27]
stl/elbow arm link v11.stl
74.0 x 16.0 x 50.0
