sicoco/Minicranebot/stl/twin servo holder.stl

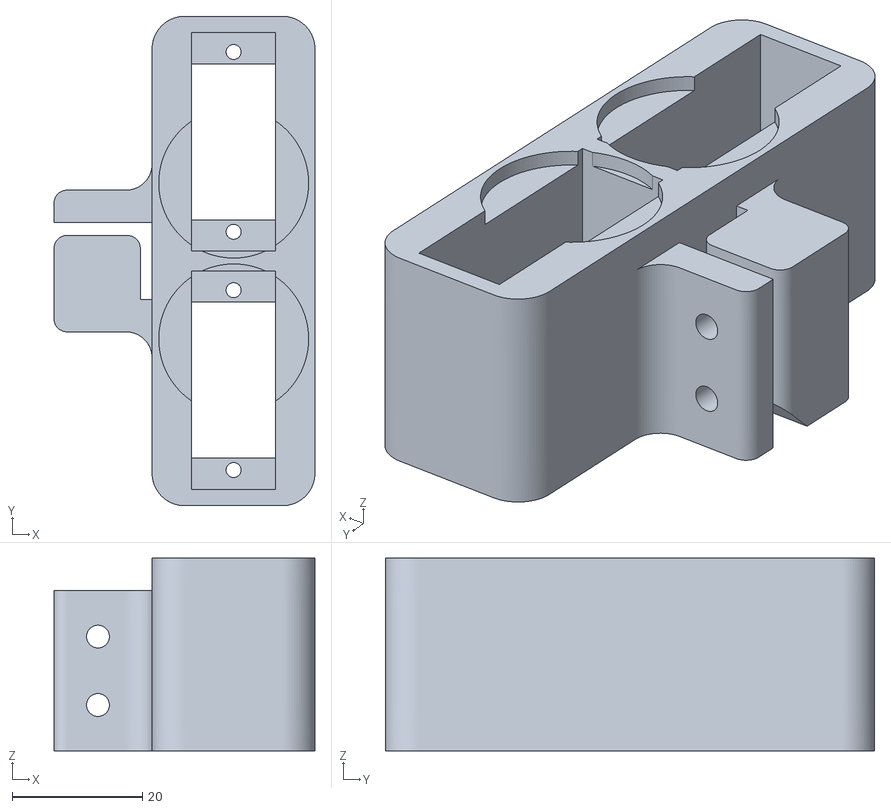
[picture p84: CAD file, 2018-07-27]
stl/twin servo holder.stl
40.0 x 75.1 x 29.6
