sicoco/Minicranebot/stl/shoulder fixture.stl

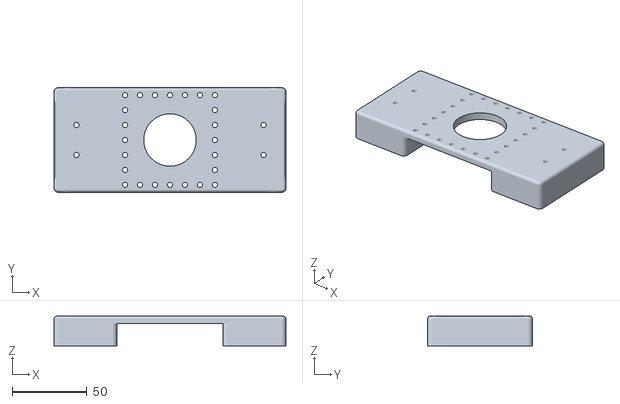
[picture p85: CAD file, 2018-07-27]
stl/shoulder fixture.stl
155.0 x 70.0 x 20.0
