sicoco/Minicranebot/stl/elbow joint v9.stl

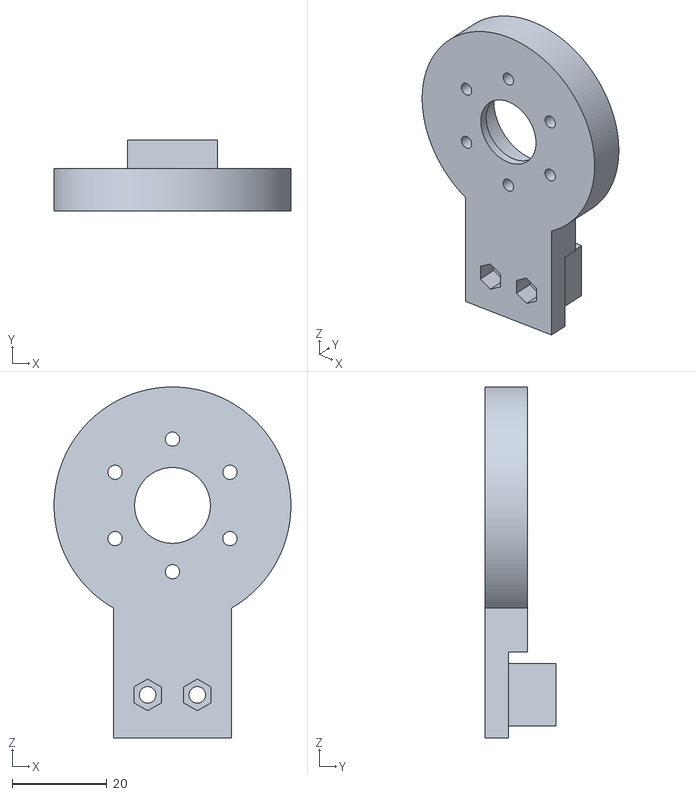
[picture p86: CAD file, 2018-07-27]
stl/elbow joint v9.stl
50.0 x 15.0 x 74.1
