sicoco/Minicranebot/stl/bowden tube holder_planetary gearbox bowden cable actuator v9_Body1_bowden tube holder v5.stl

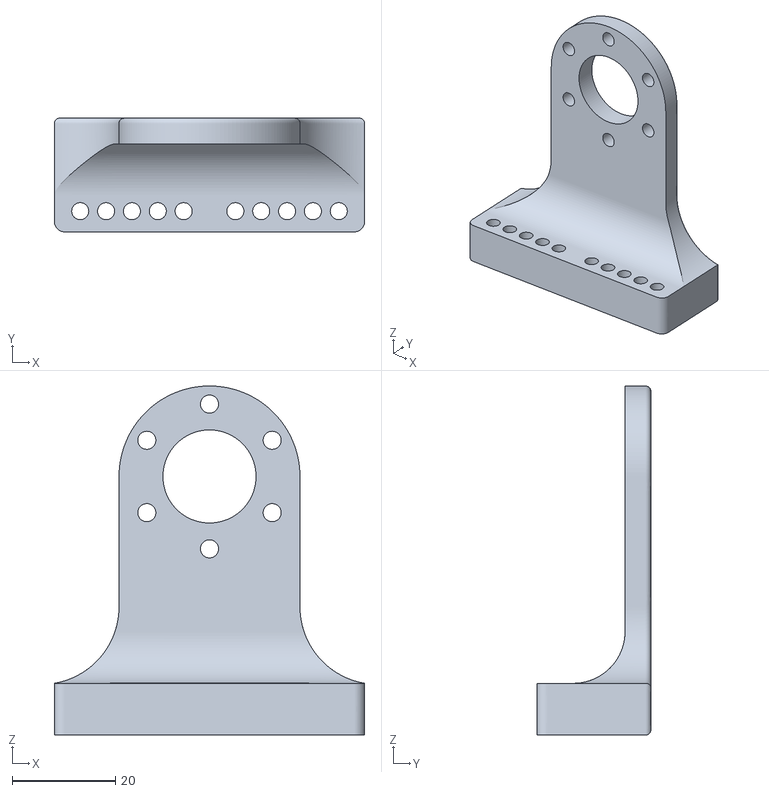
[picture p87: CAD file, 2018-07-27]
stl/bowden tube holder_planetary gearbox bowden cable actuator v9_Body1_bowden tube holder v5.stl
60.0 x 22.0 x 67.5
