sicoco/Minicranebot/stl/arm (1).stl

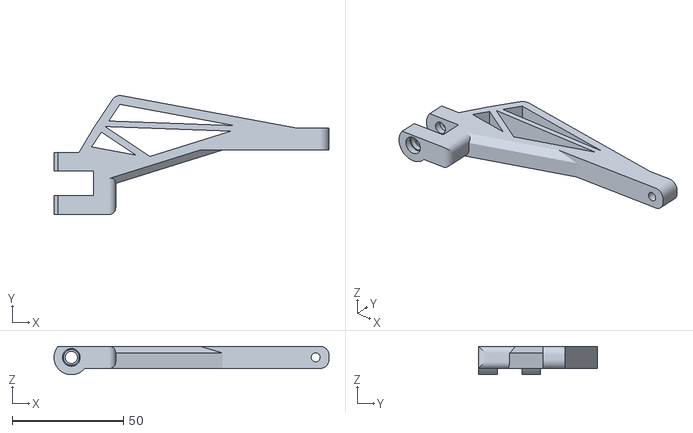
[picture p88: CAD file, 2018-07-27]
stl/arm (1).stl
123.8 x 53.6 x 12.8
