sicoco/Minicranebot/stl/cap.stl

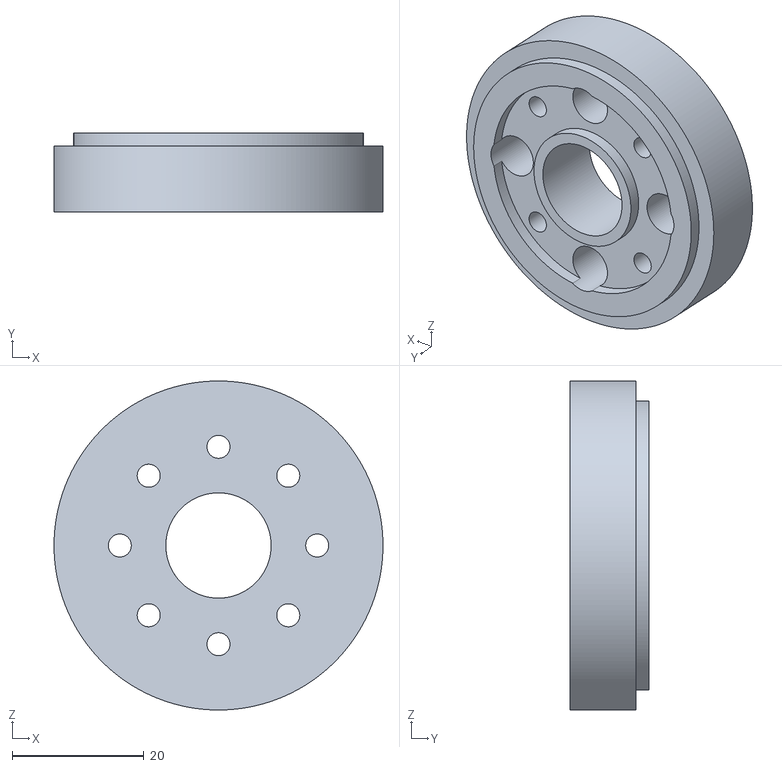
[picture p89: CAD file, 2018-07-27]
stl/cap.stl
50.0 x 12.0 x 50.0
