sicoco/Minicranebot/stl/counterweightbase.stl

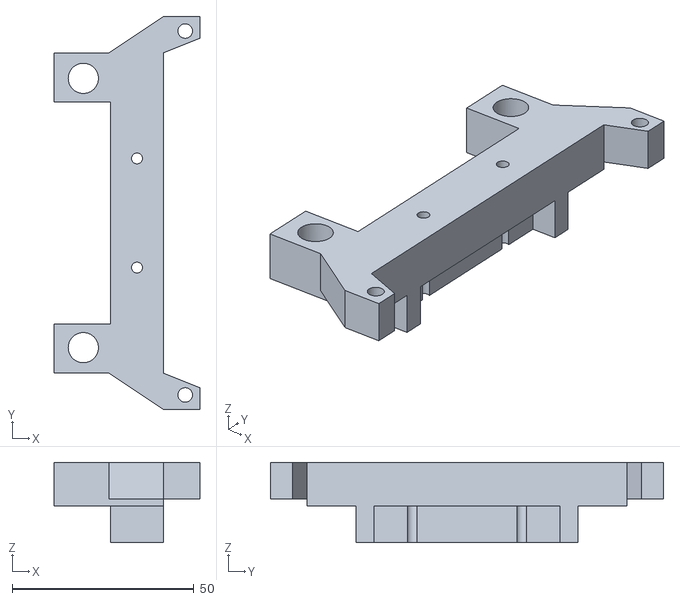
[picture p90: CAD file, 2018-07-27]
stl/counterweightbase.stl
40.0 x 108.0 x 22.0
