sicoco/Minicranebot/stl/backpack.stl

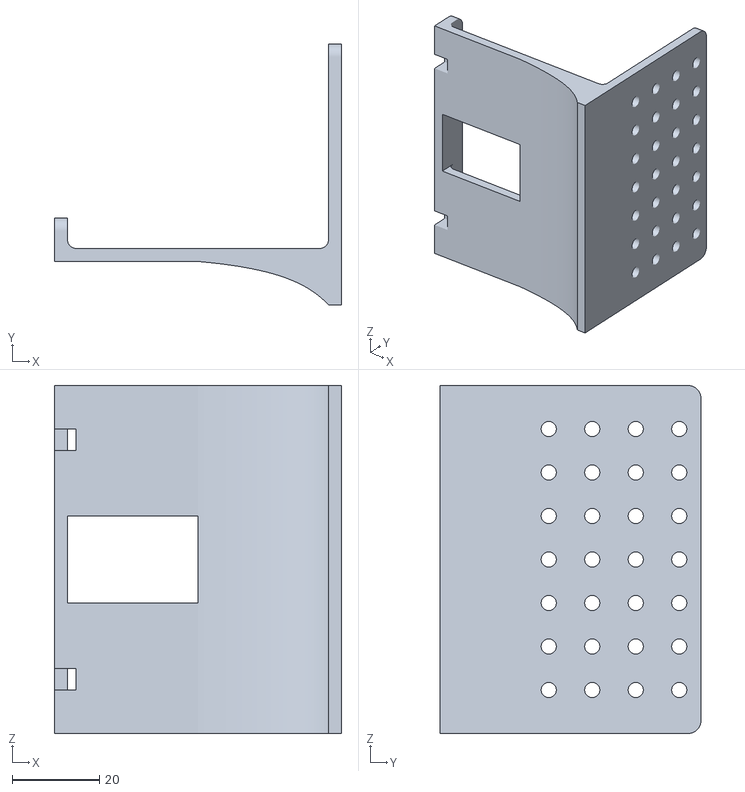
[picture p91: CAD file, 2018-07-27]
stl/backpack.stl
66.0 x 60.0 x 80.0
