sicoco/Minicranebot/stl/backpack hook v3.stl

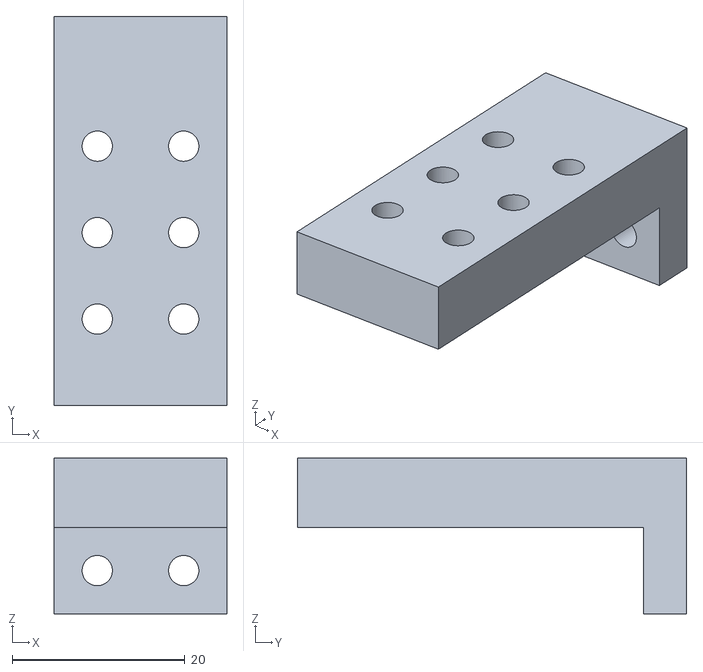
[picture p92: CAD file, 2018-07-27]
stl/backpack hook v3.stl
20.0 x 45.0 x 18.0
