sicoco/Minicranebot/stl/pulley cap.stl

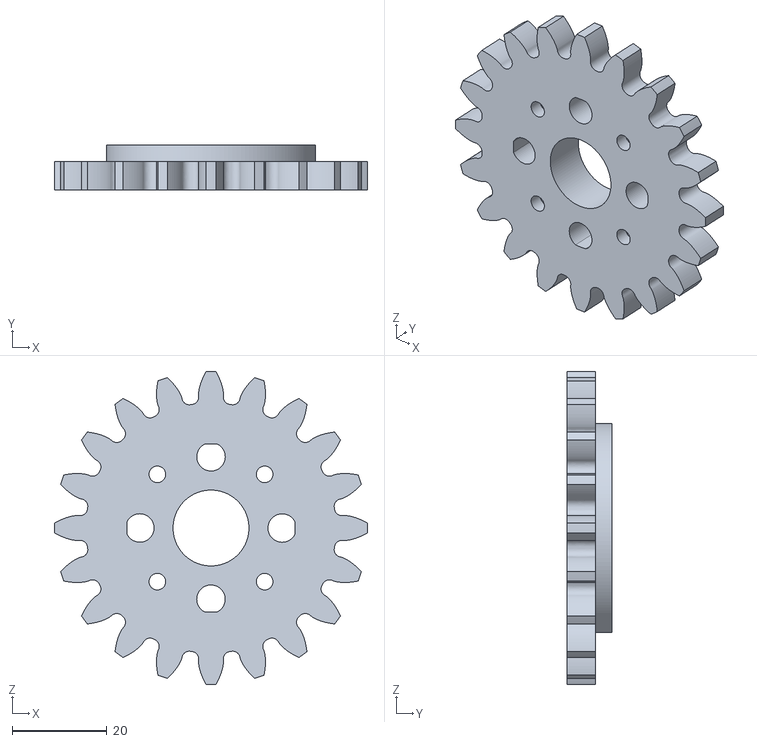
[picture p93: CAD file, 2018-07-27]
stl/pulley cap.stl
66.0 x 9.50 x 66.0
