sicoco/Minicranebot/stl/flexible finger.stl

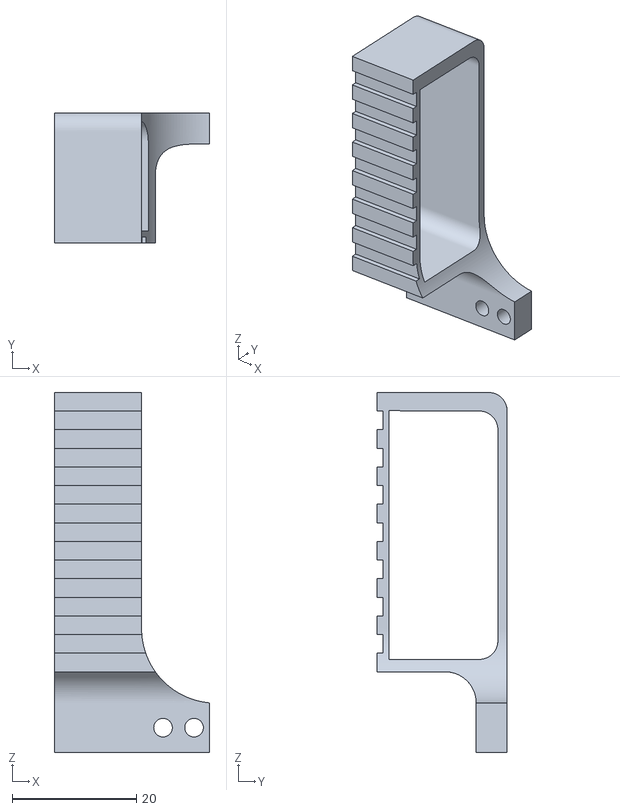
[picture p94: CAD file, 2018-07-27]
stl/flexible finger.stl
25.0 x 21.0 x 58.0
