sicoco/Minicranebot/stl/Spur Gear (50 teeth).stl

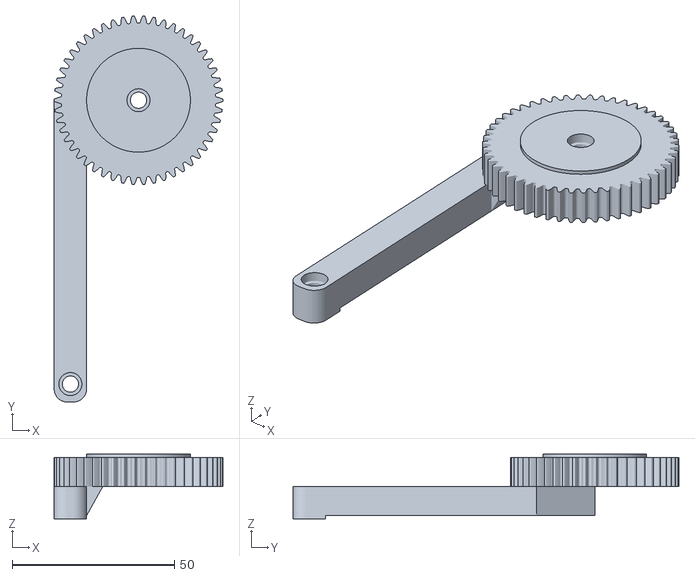
[picture p95: CAD file, 2018-07-27]
stl/Spur Gear (50 teeth).stl
52.0 x 119.0 x 20.0
