sicoco/Minicranebot/stl/shoulder fixture2.stl

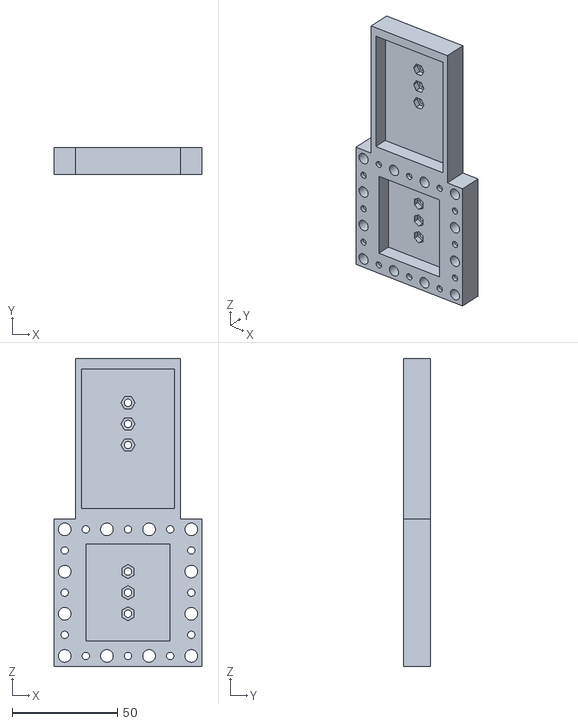
[picture p96: CAD file, 2018-07-27]
stl/shoulder fixture2.stl
70.0 x 13.0 x 146.0
