sicoco/Minicranebot/stl/counterweight base plate v14.stl

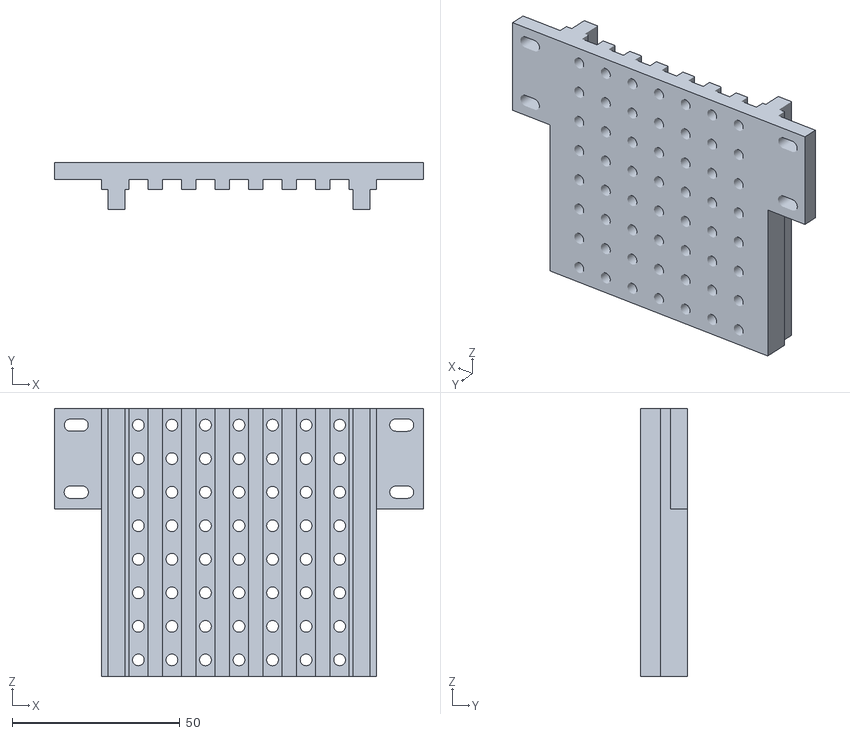
[picture p97: CAD file, 2018-07-27]
stl/counterweight base plate v14.stl
110.0 x 14.0 x 80.0
