sicoco/Minicranebot/stl/front extention shield.stl

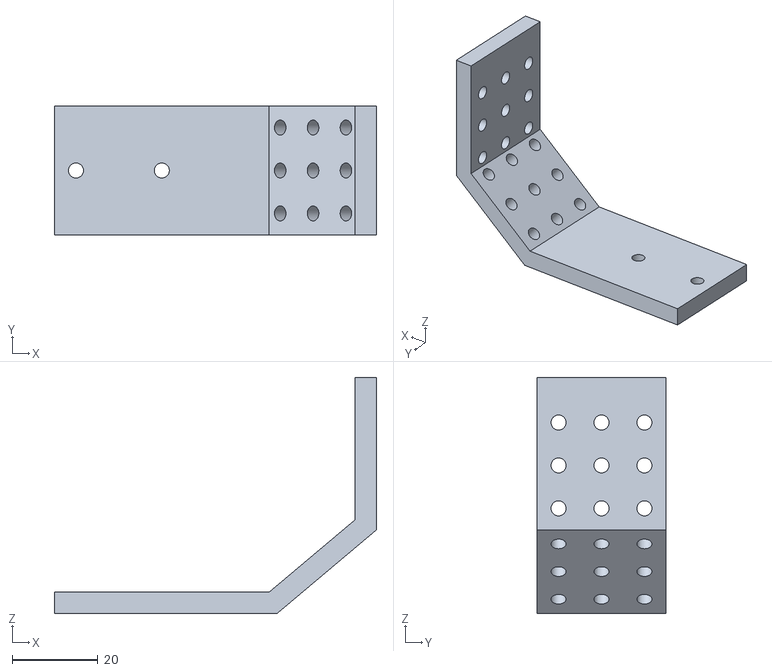
[picture p98: CAD file, 2018-07-27]
stl/front extention shield.stl
75.0 x 30.0 x 55.0
