sicoco/Minicranebot/stl/block finger.stl

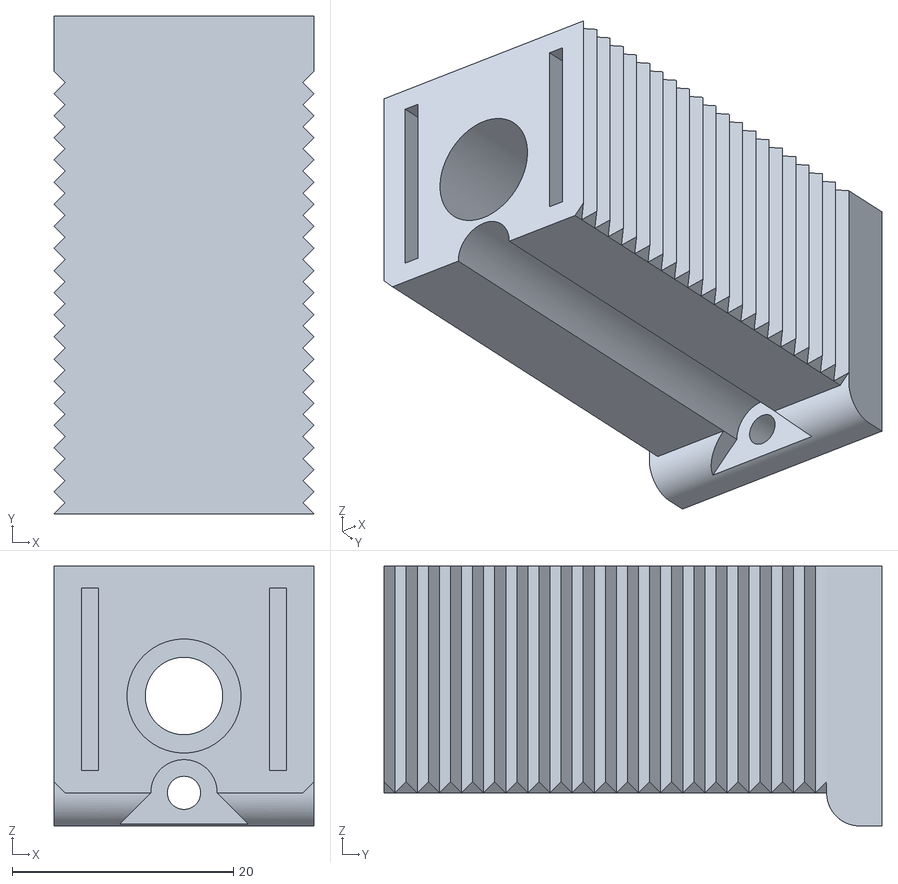
[picture p99: CAD file, 2018-07-27]
stl/block finger.stl
23.5 x 45.0 x 23.5
