sicoco/Minicranebot/stl/gear fixture.stl

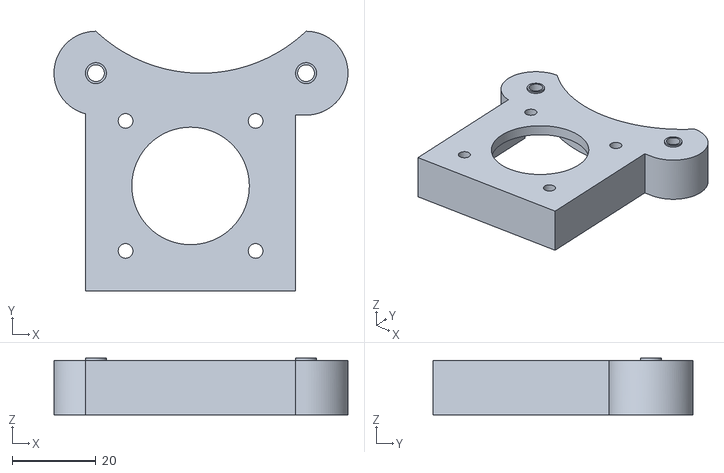
[picture p100: CAD file, 2018-07-27]
stl/gear fixture.stl
70.1 x 61.9 x 13.5
