sicoco/Minicranebot/stl/bearing holder.stl

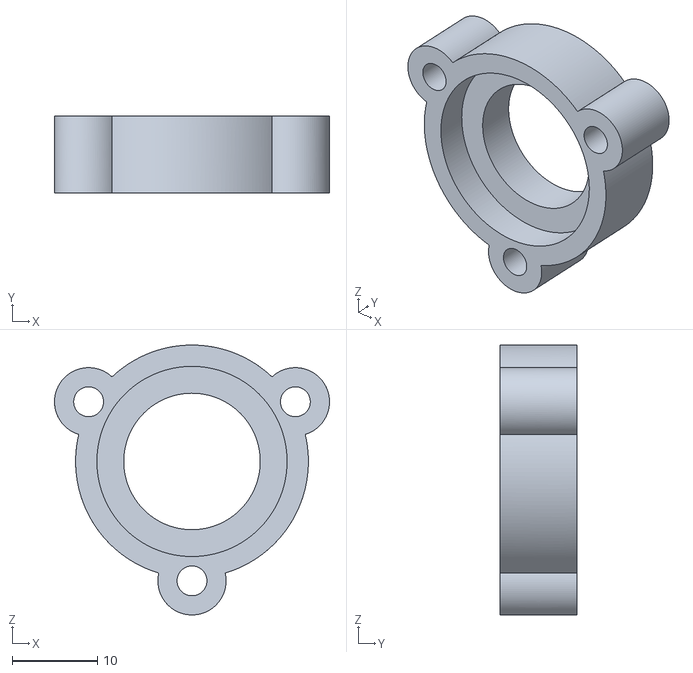
[picture p101: CAD file, 2018-07-27]
stl/bearing holder.stl
32.2 x 9.00 x 31.7
