sicoco/Minicranebot/stl/fingertip.stl

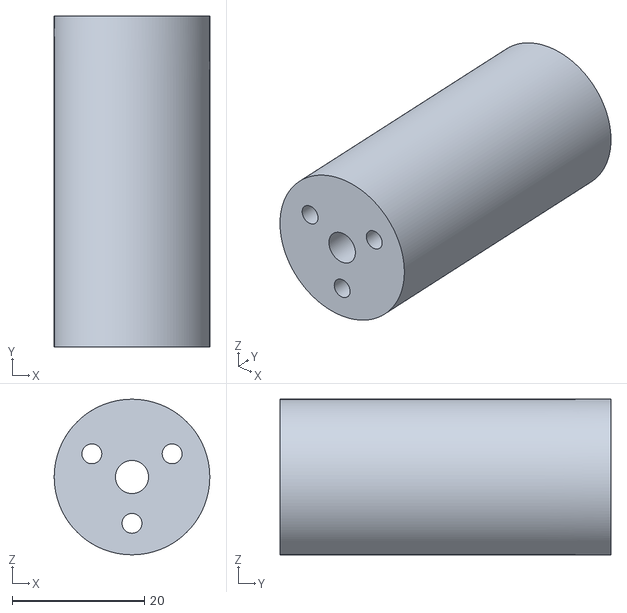
[picture p102: CAD file, 2018-07-27]
stl/fingertip.stl
23.5 x 50.0 x 23.5
