sicoco/Minicranebot/stl/rack.stl

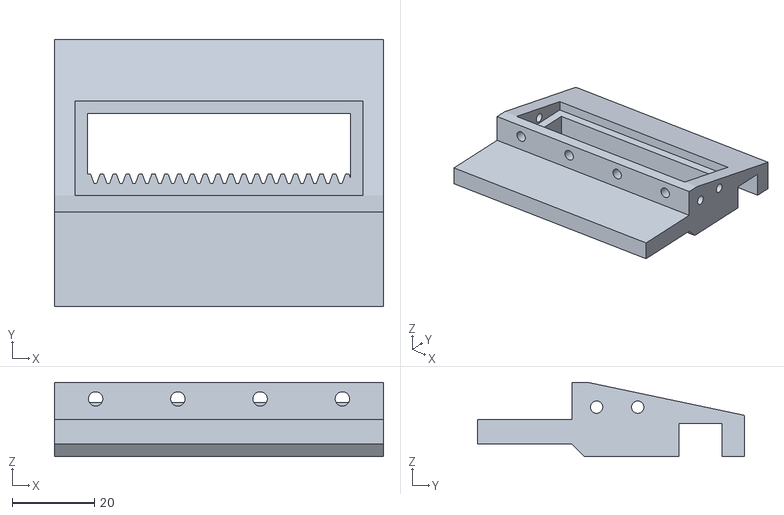
[picture p103: CAD file, 2018-07-27]
stl/rack.stl
80.0 x 65.0 x 18.0
