sicoco/Minicranebot/stl/gearbox separator.stl

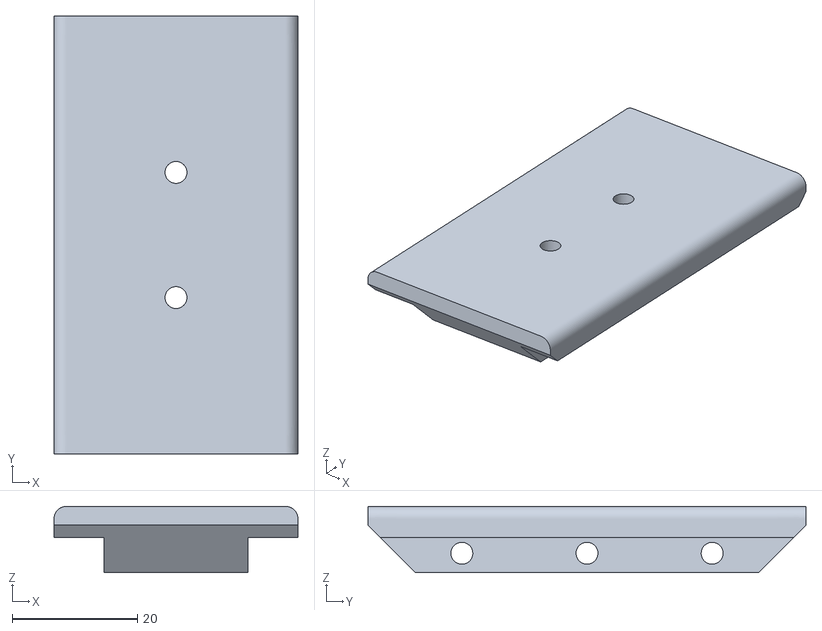
[picture p104: CAD file, 2018-07-27]
stl/gearbox separator.stl
39.0 x 70.0 x 10.6
