sicoco/Minicranebot/stl/finger rack.stl

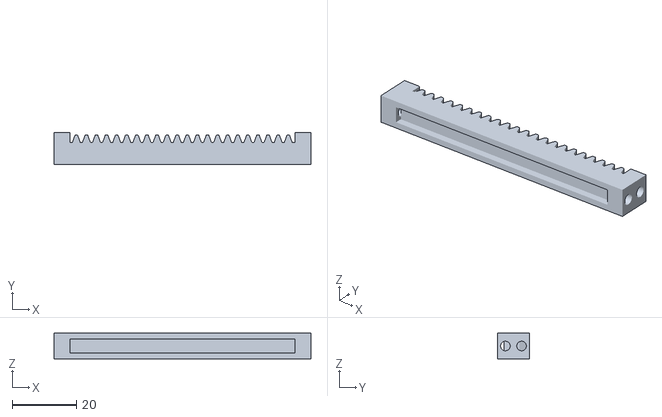
[picture p105: CAD file, 2018-07-27]
stl/finger rack.stl
80.0 x 10.0 x 8.00
