sicoco/Minicranebot/stl/fingertip cap.stl

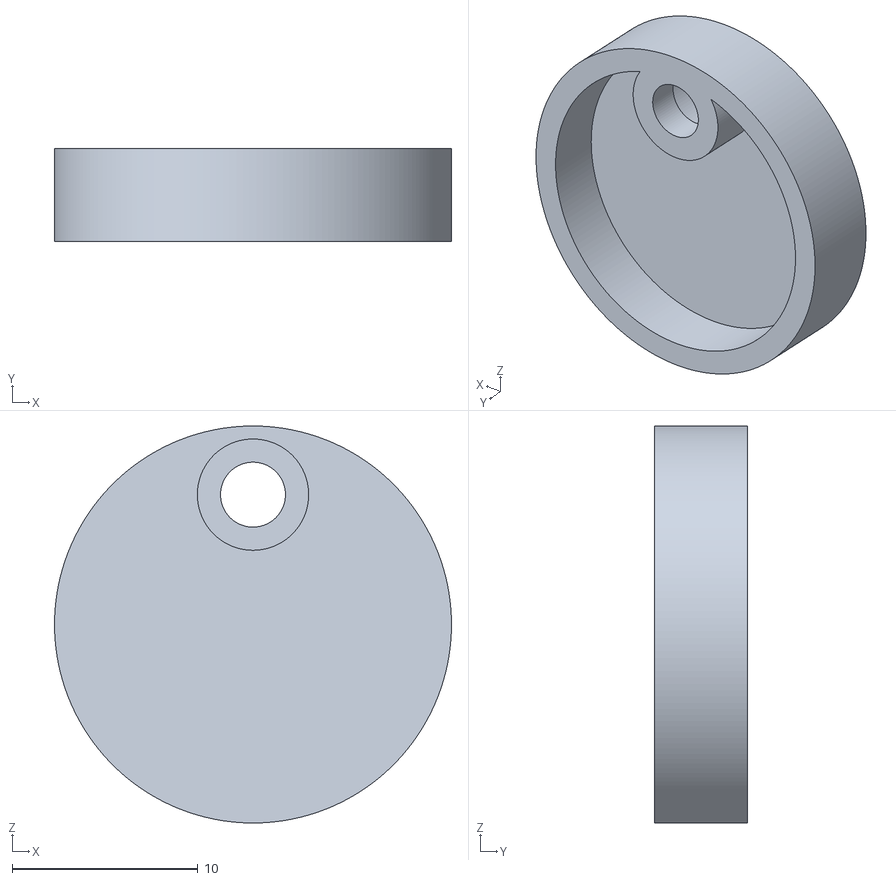
[picture p106: CAD file, 2018-07-27]
stl/fingertip cap.stl
21.4 x 5.00 x 21.4
