sicoco/Minicranebot/stl/servo holder.stl

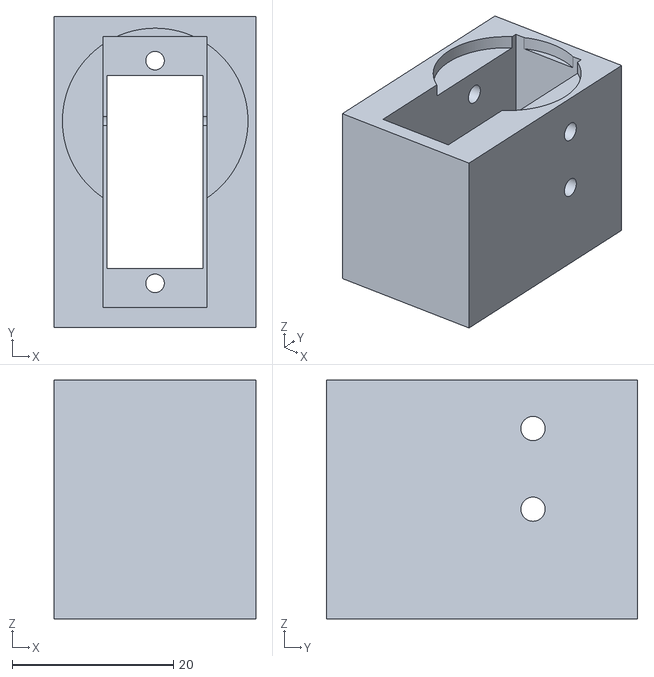
[picture p107: CAD file, 2018-07-27]
stl/servo holder.stl
25.0 x 38.5 x 29.6
