sicoco/Minicranebot/stl/bearing holder2.stl

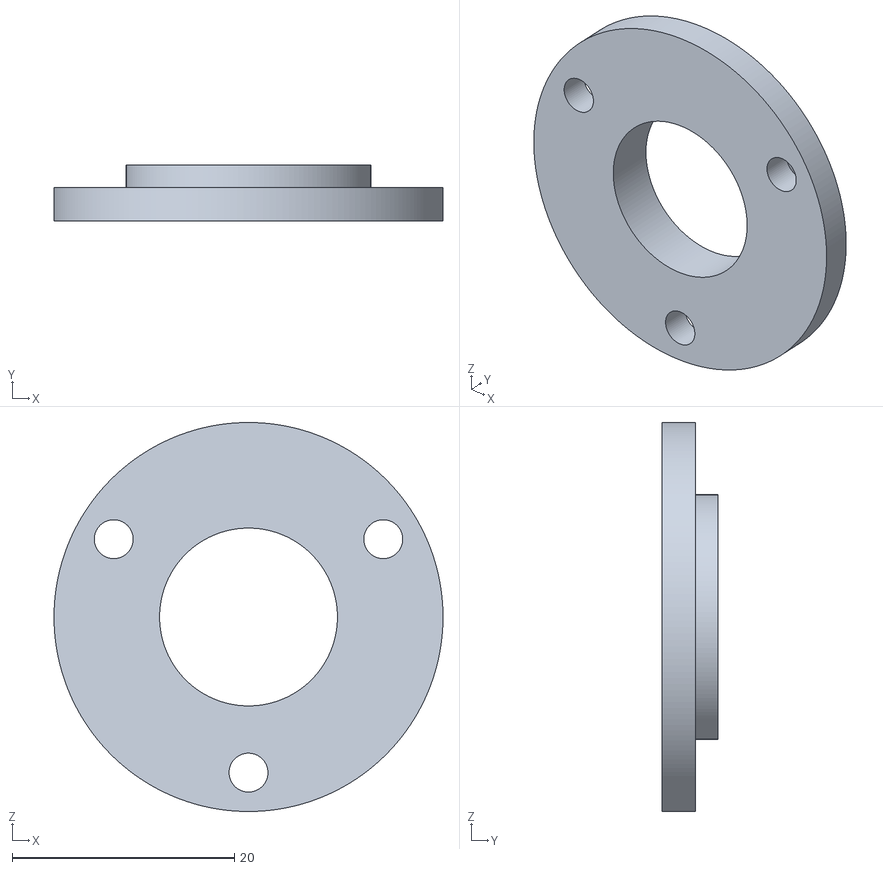
[picture p108: CAD file, 2018-07-27]
stl/bearing holder2.stl
35.0 x 5.00 x 35.0
