sicoco/Minicranebot/stl/14T M1 Spur gear v4.stl

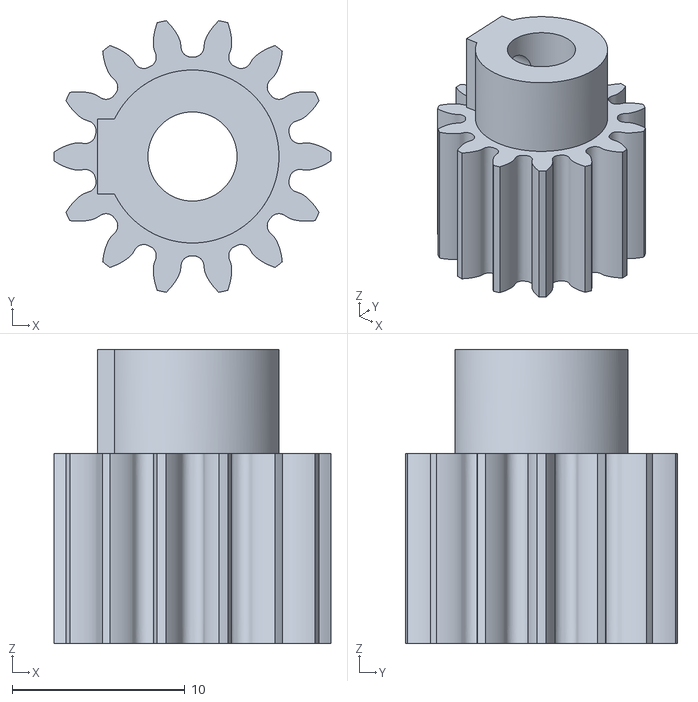
[picture p109: CAD file, 2018-07-27]
stl/14T M1 Spur gear v4.stl
16.0 x 15.7 x 17.0
