sicoco/Minicranebot/stl/42 stepper motor fixture spacer 2mm.stl

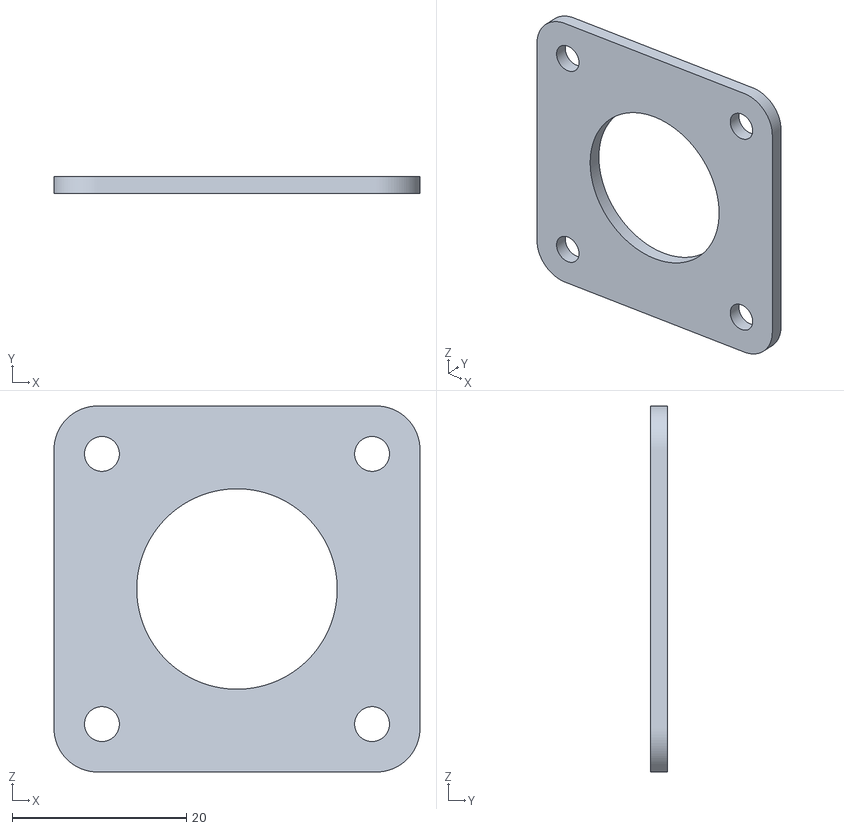
[picture p110: CAD file, 2018-07-27]
stl/42 stepper motor fixture spacer 2mm.stl
42.0 x 2.00 x 42.0
